Sadrita404/16-Key-Macro-Pad/IMAGES/6.png

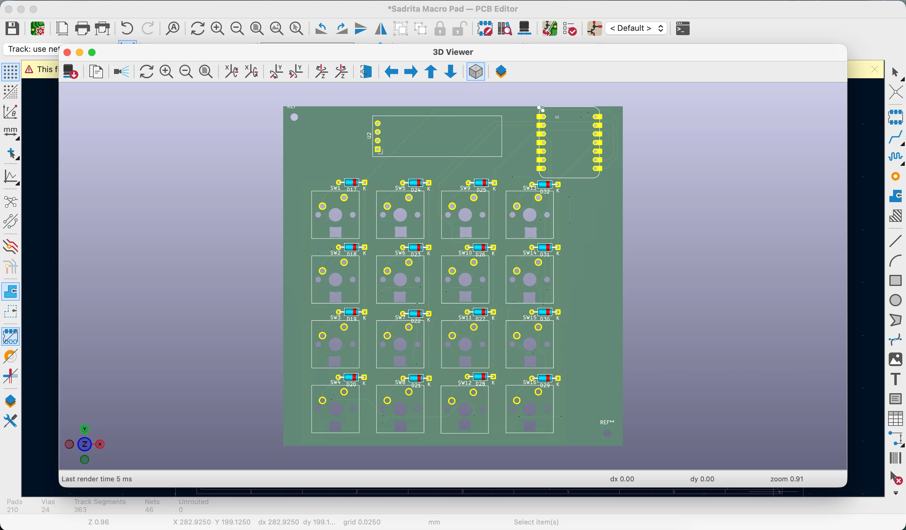
IMAGES/6.png
