Sadrita404/16-Key-Macro-Pad/IMAGES/7.png

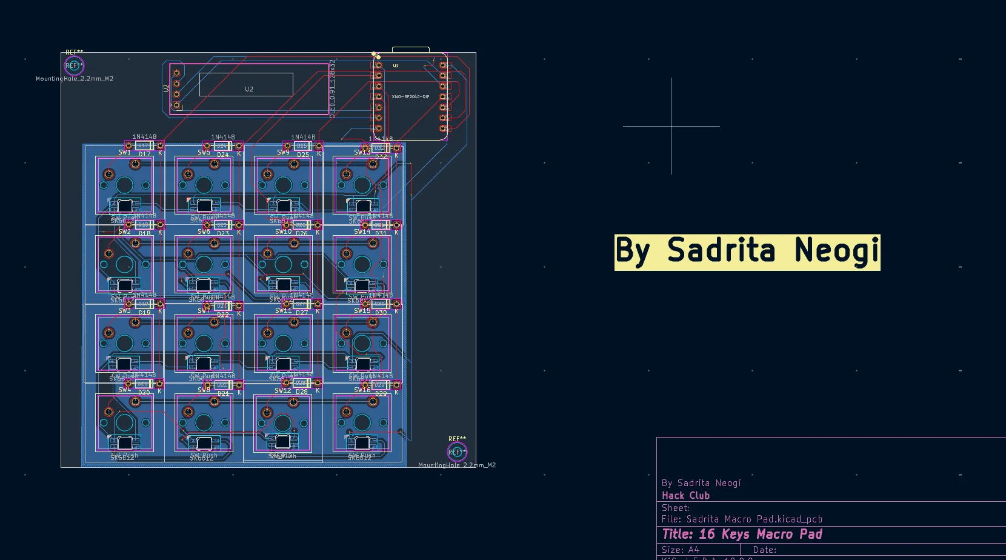
IMAGES/7.png
