Sadrita404/16-Key-Macro-Pad/BILL/1 Bill.png

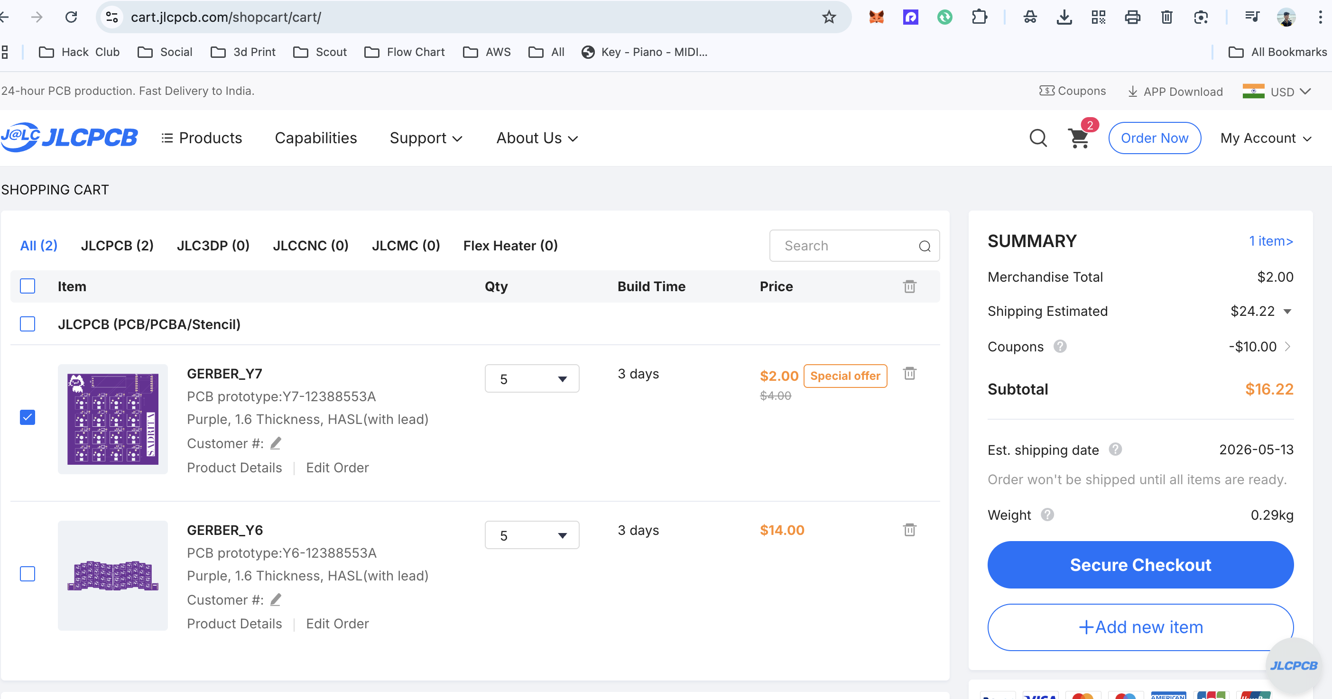
BILL/1 Bill.png
