Sadrita404/16-Key-Macro-Pad/BILL/2 Bill.png

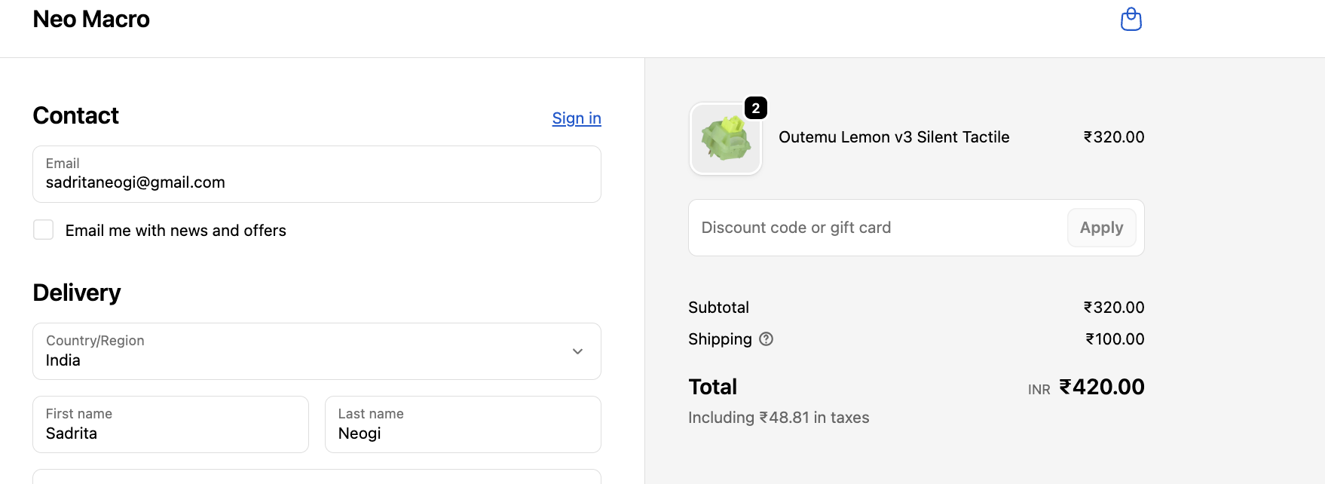
BILL/2 Bill.png
