Sadrita404/16-Key-Macro-Pad/BILL/3 Bill.png

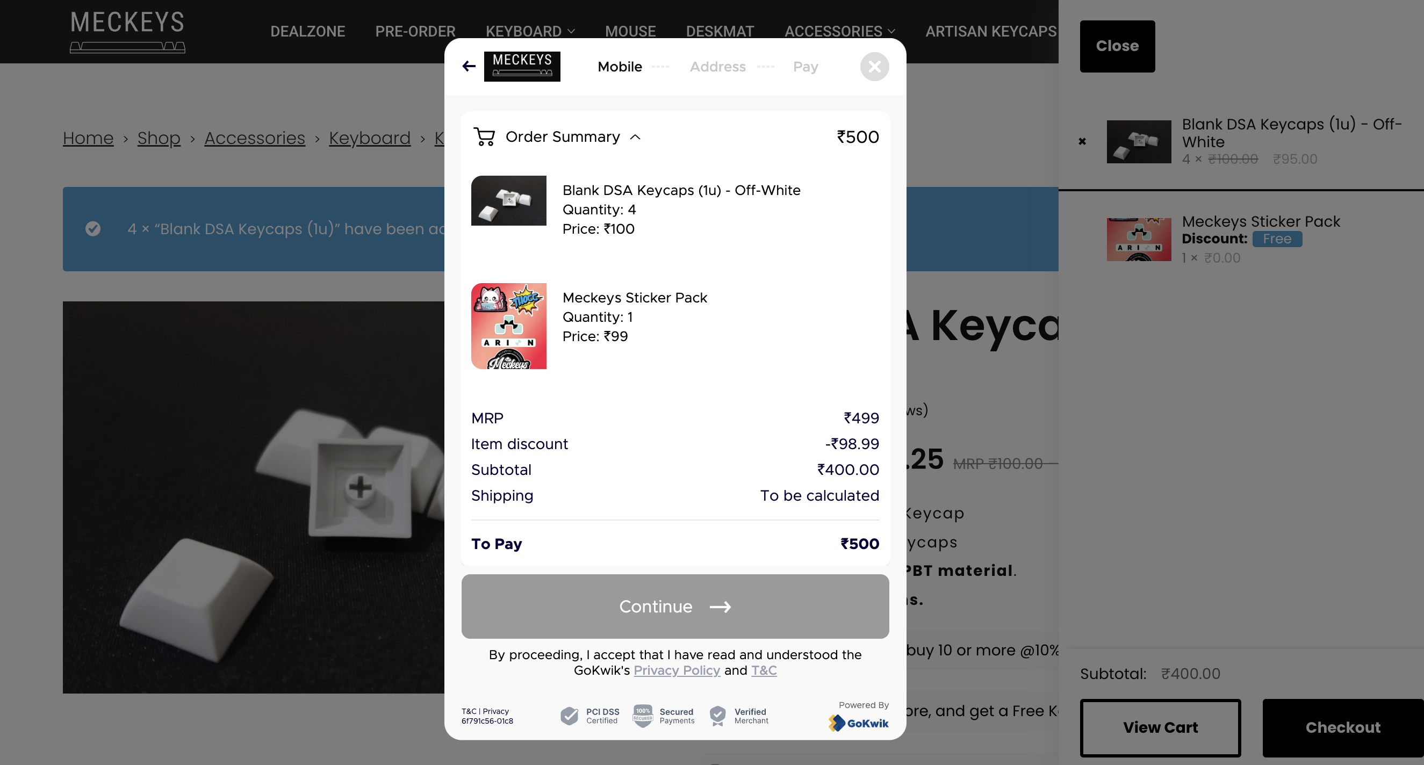
BILL/3 Bill.png
