Sadrita404/16-Key-Macro-Pad/BILL/4 Bill.png

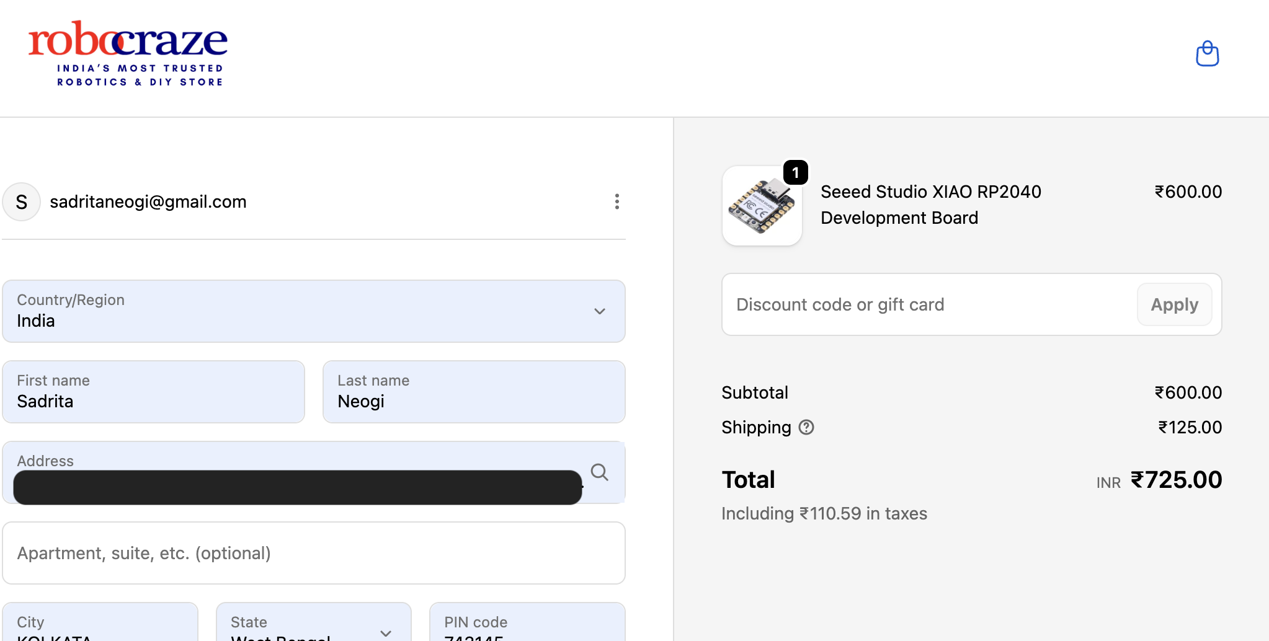
BILL/4 Bill.png
