Sadrita404/16-Key-Macro-Pad/BILL/5 Bill.png

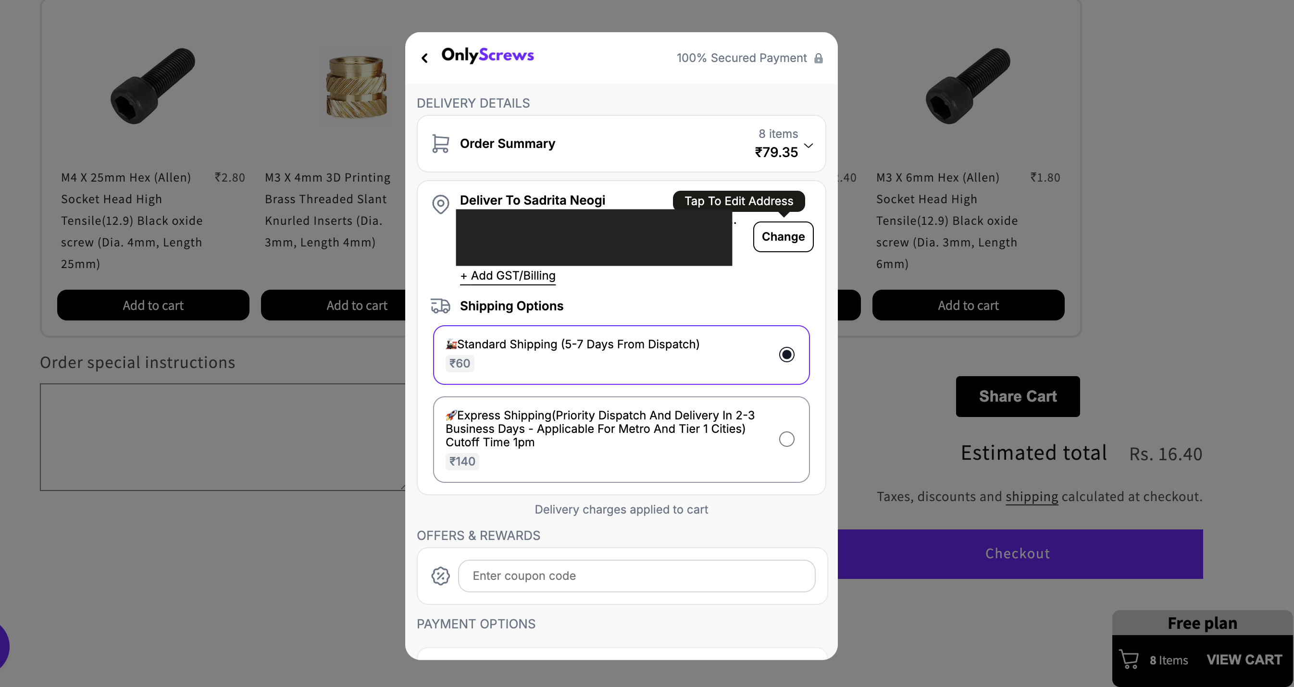
BILL/5 Bill.png
