Sadrita404/16-Key-Macro-Pad/BILL/6 Bill.png

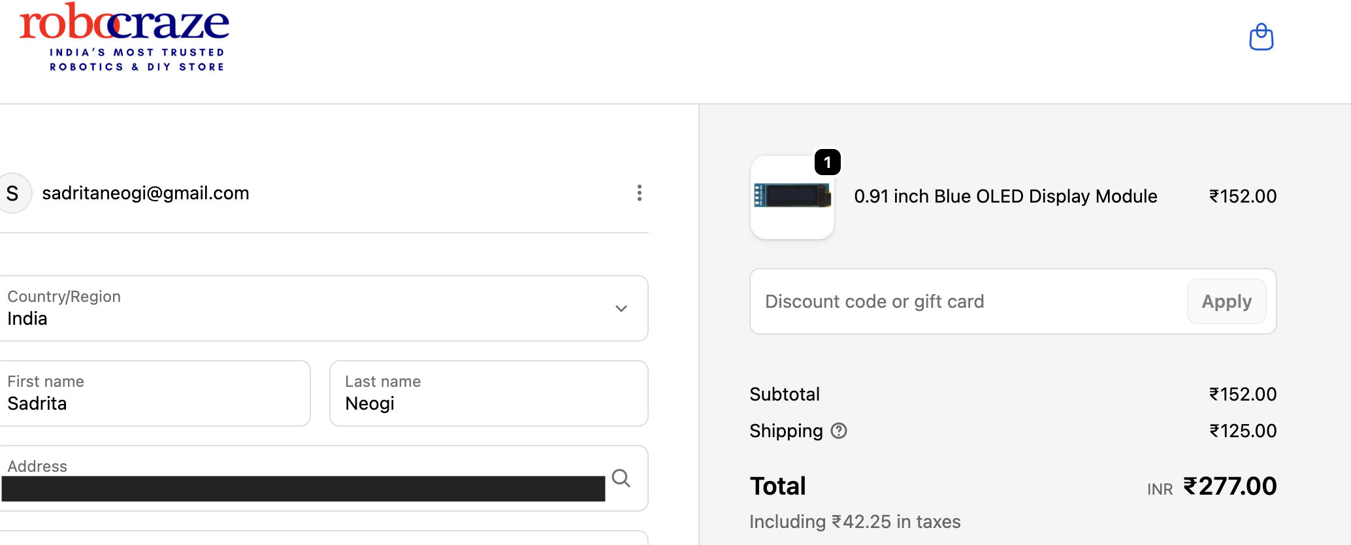
BILL/6 Bill.png
