Sadrita404/16-Key-Macro-Pad/BILL/7 Bill.png

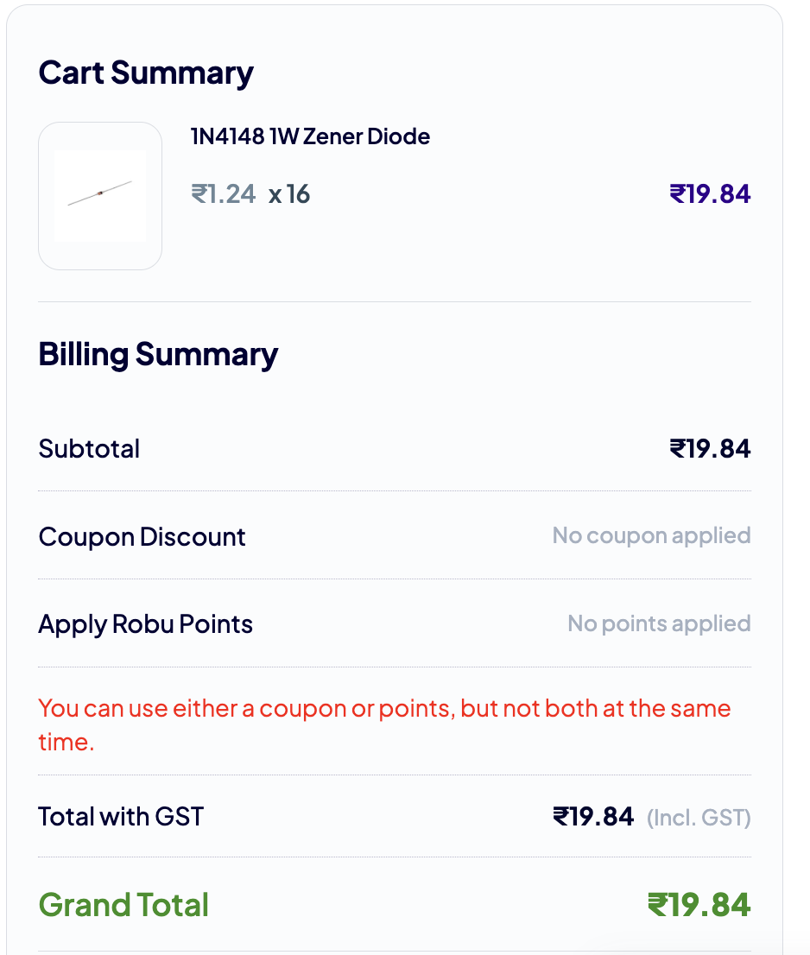
BILL/7 Bill.png
