Sadrita404/16-Key-Macro-Pad/IMAGES/1.png

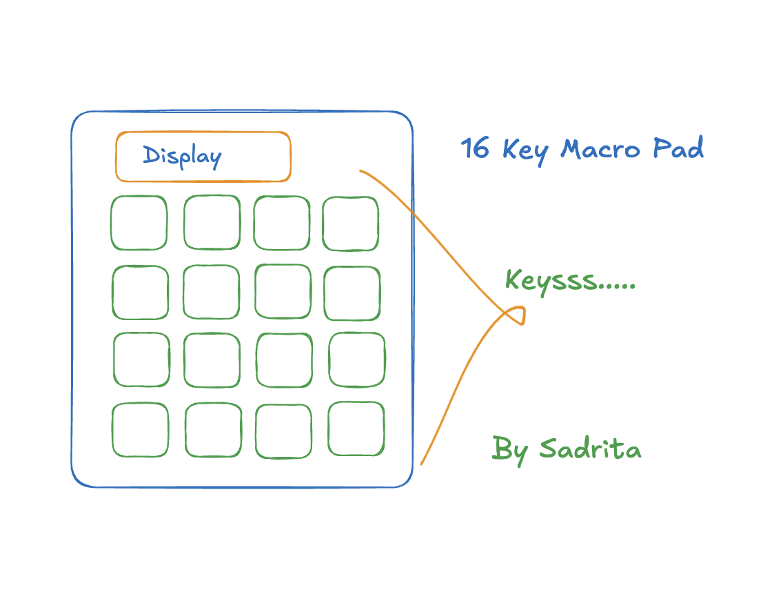
IMAGES/1.png
