Sadrita404/16-Key-Macro-Pad/IMAGES/2.png

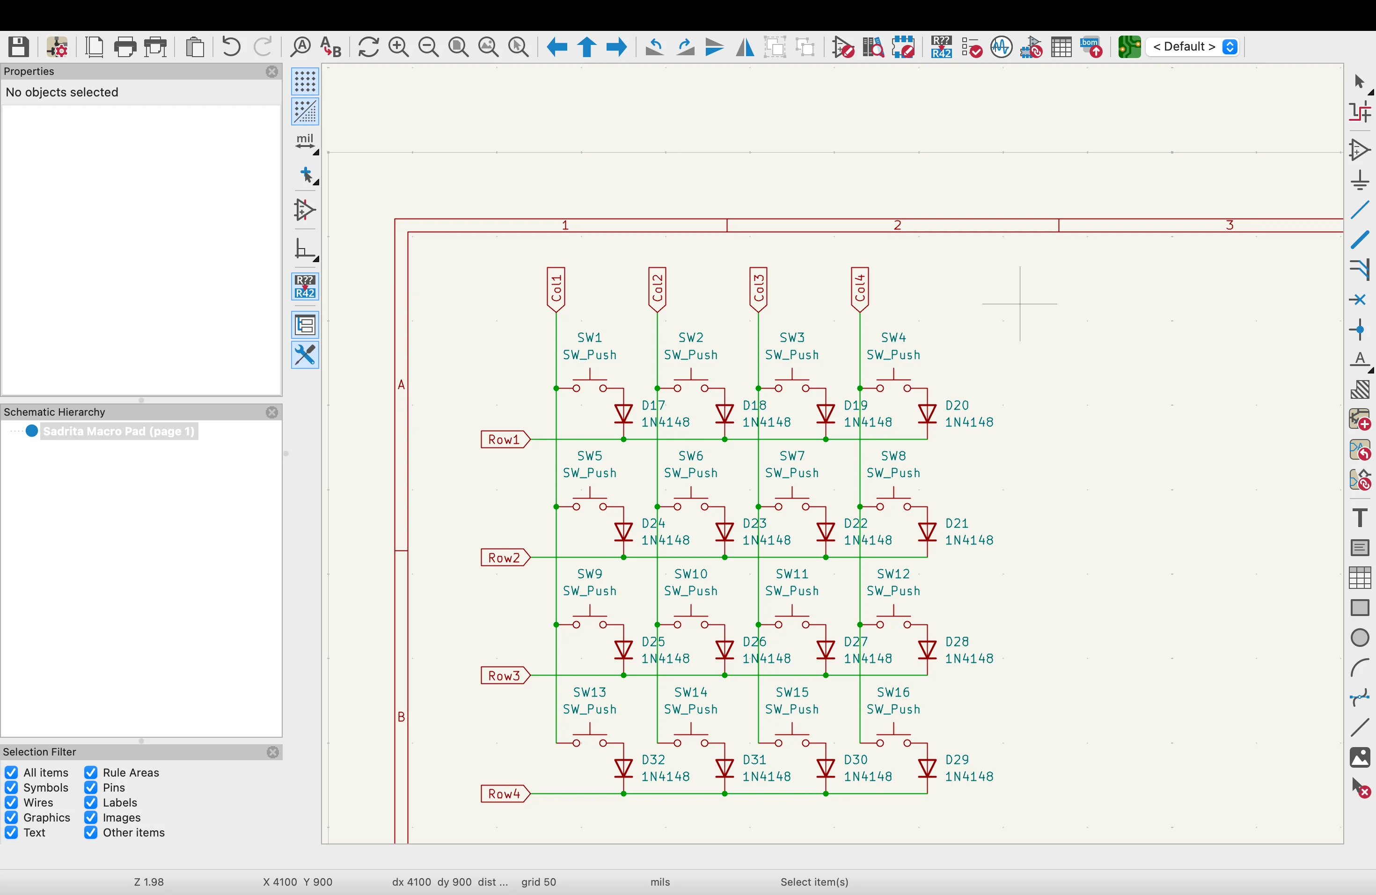
IMAGES/2.png
