Sadrita404/16-Key-Macro-Pad/IMAGES/3.png

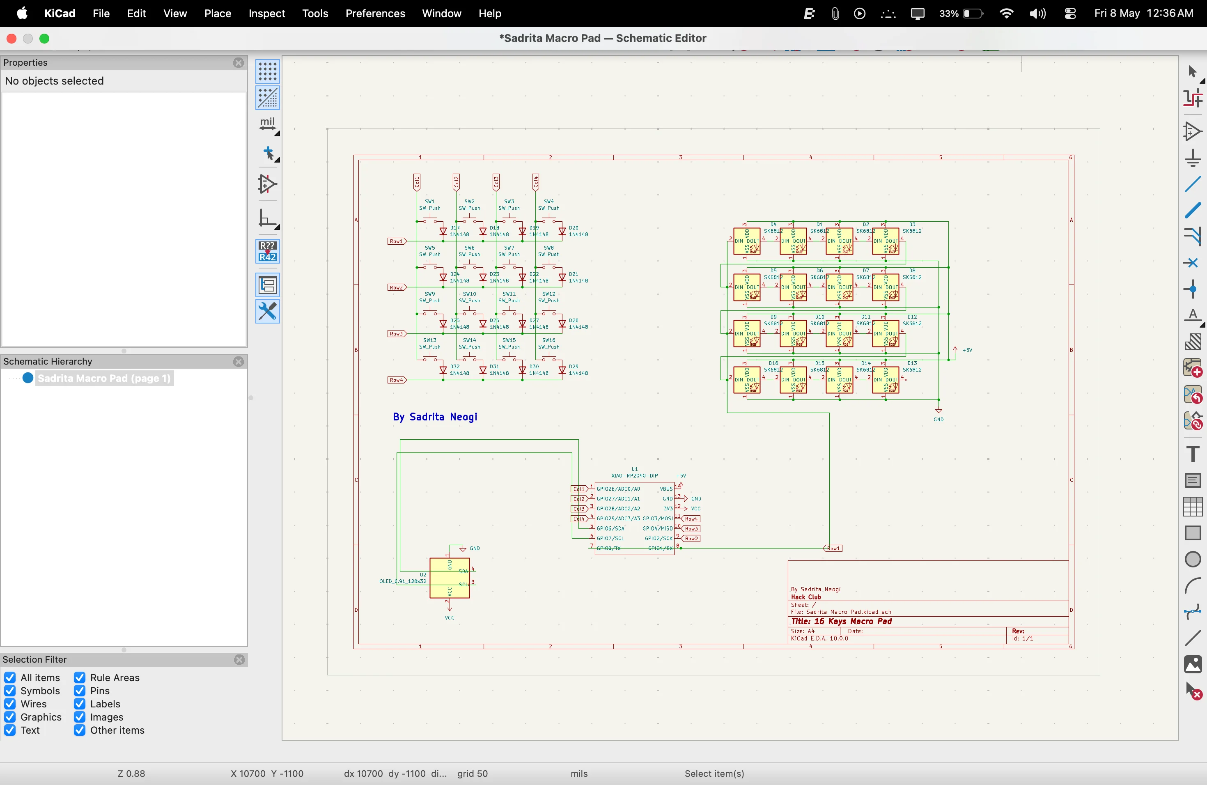
IMAGES/3.png
