Sadrita404/16-Key-Macro-Pad/IMAGES/4.png

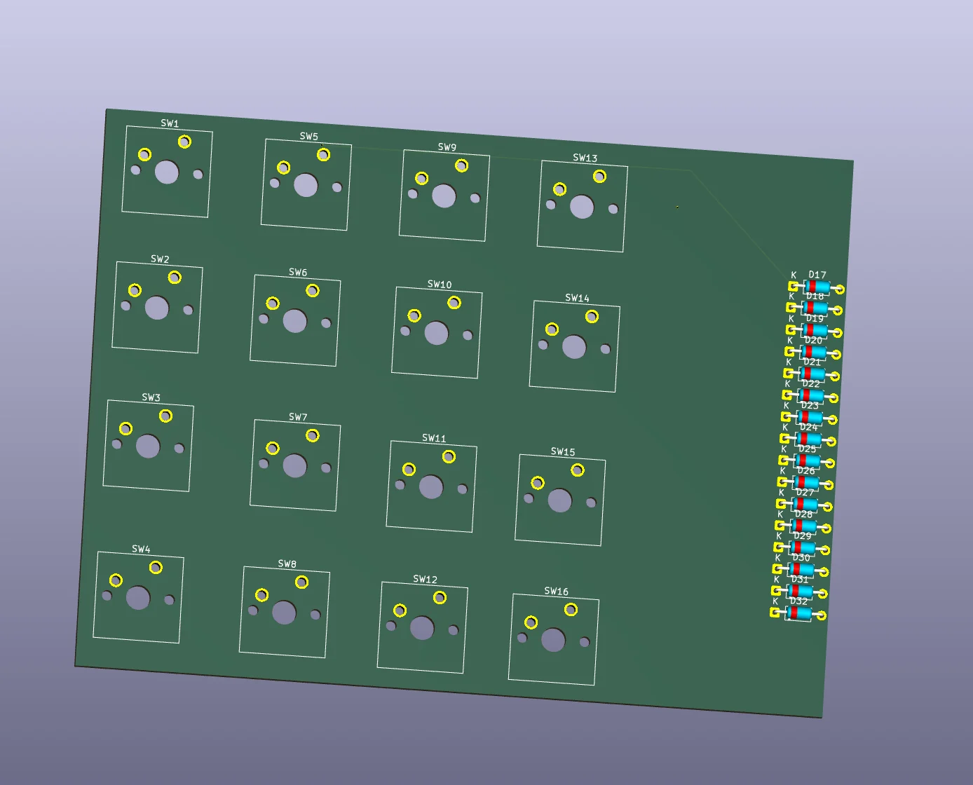
IMAGES/4.png
