Sadrita404/16-Key-Macro-Pad/IMAGES/5.png

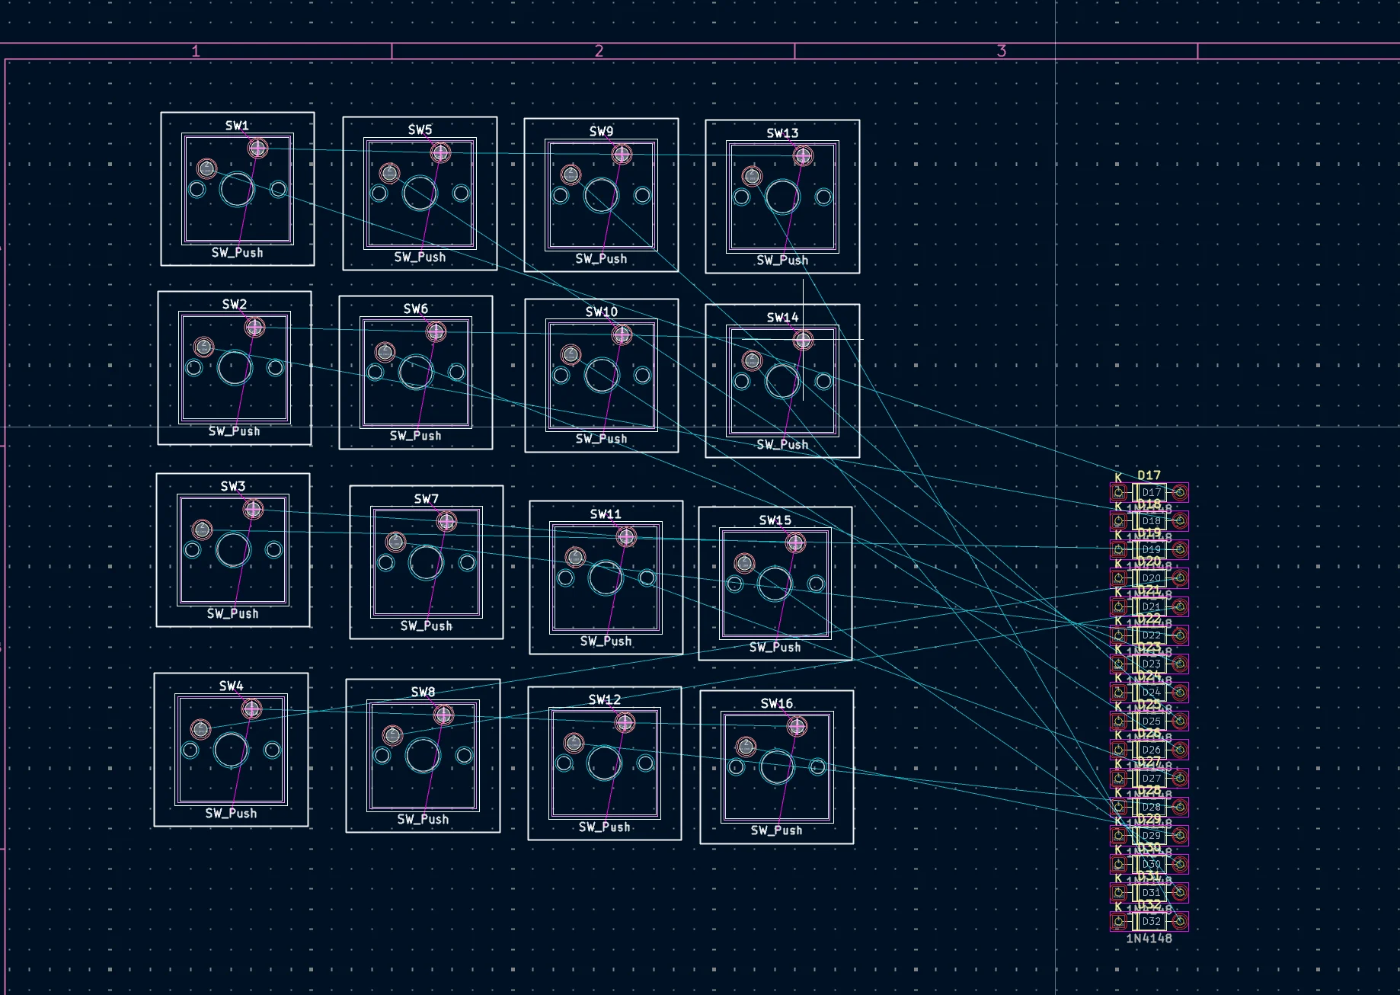
IMAGES/5.png
