Sadrita404/16-Key-Macro-Pad/IMAGES/8.png

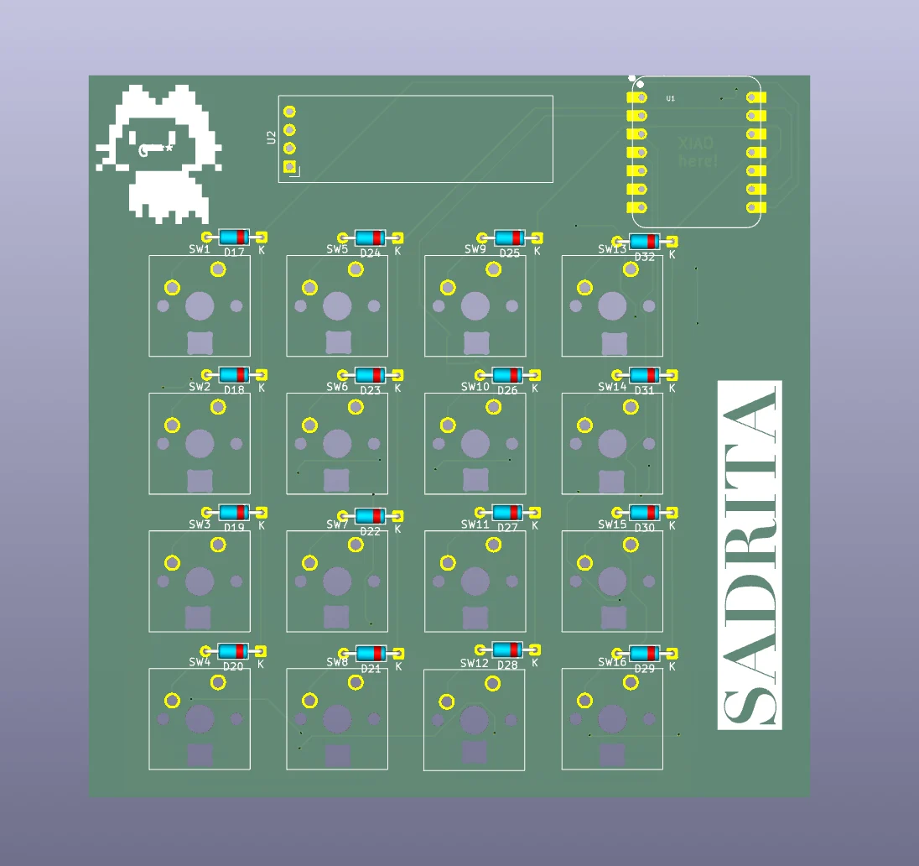
IMAGES/8.png
