Sadrita404/16-Key-Macro-Pad/IMAGES/9.png

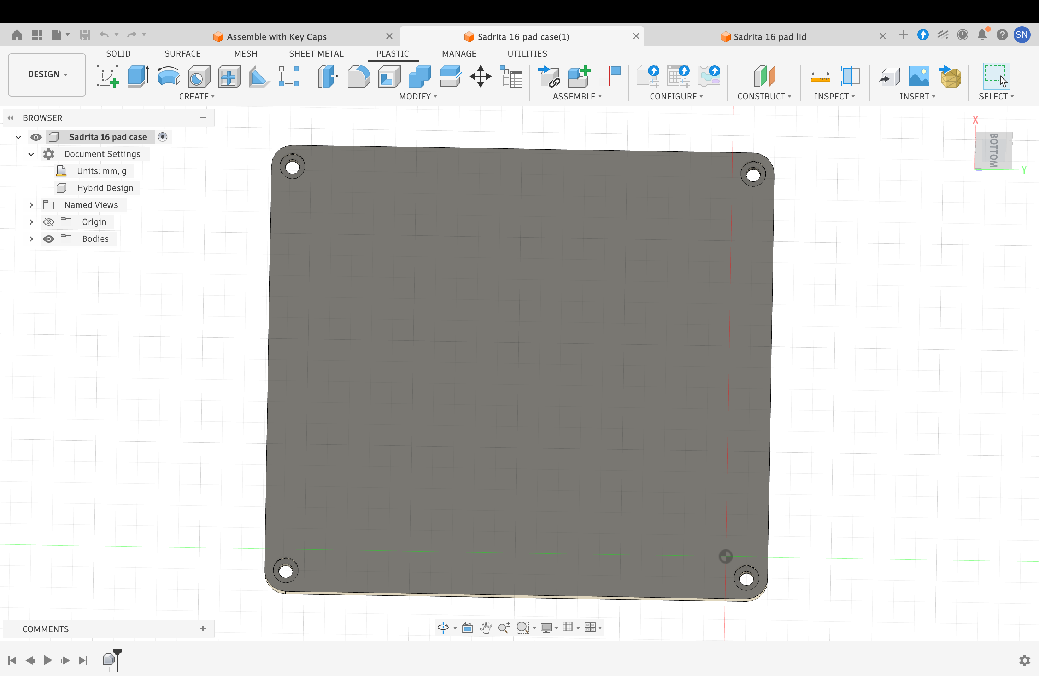
IMAGES/9.png
