Sadrita404/16-Key-Macro-Pad/IMAGES/10.png

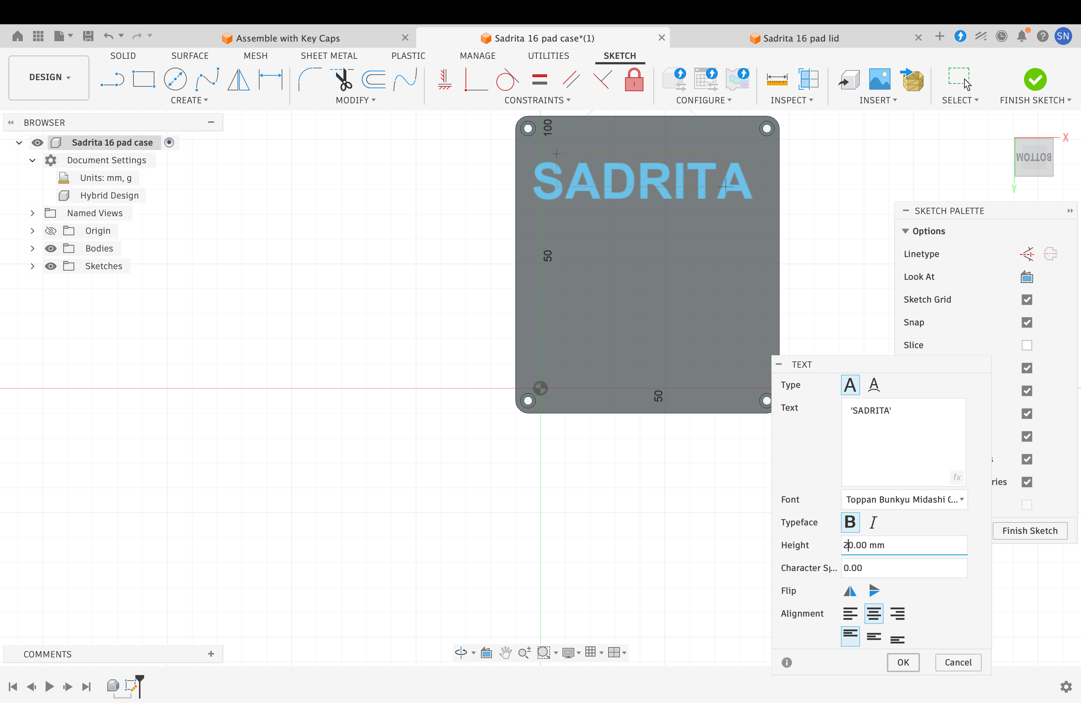
IMAGES/10.png
