Sadrita404/16-Key-Macro-Pad/IMAGES/11.png

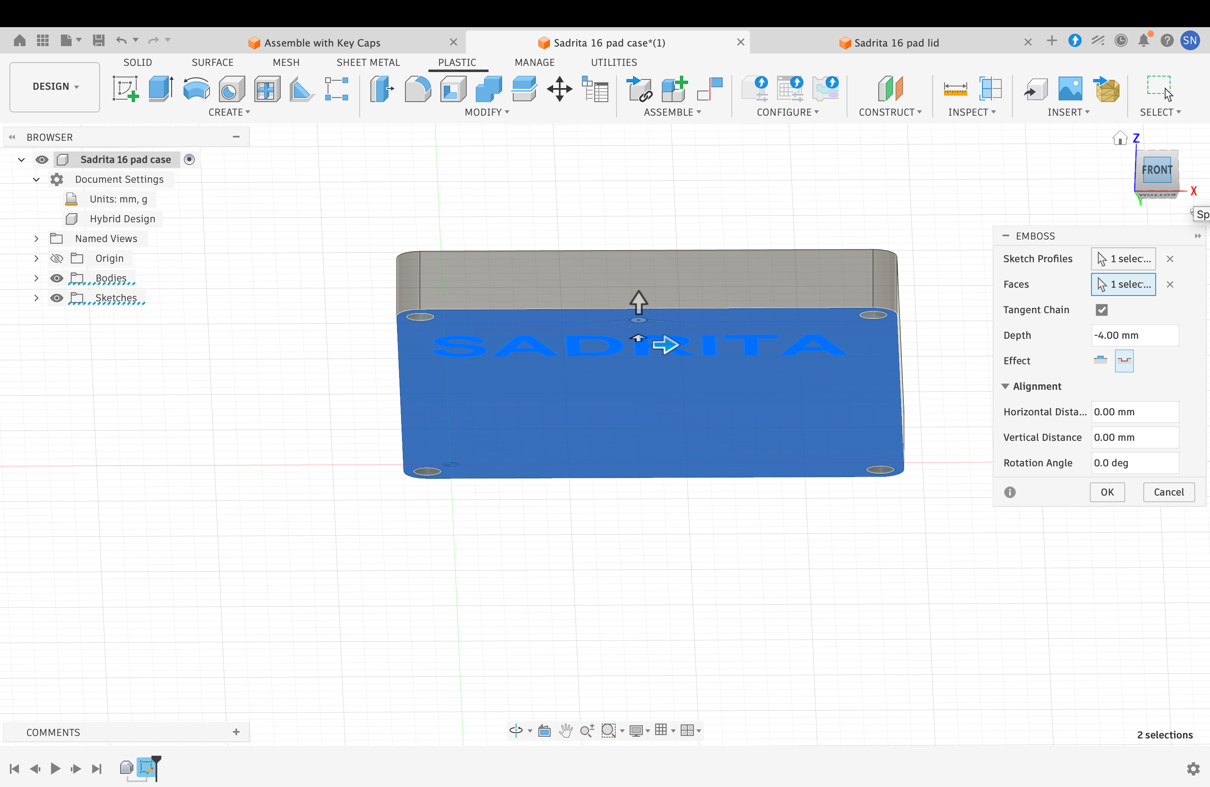
IMAGES/11.png
