Sadrita404/16-Key-Macro-Pad/IMAGES/12.png

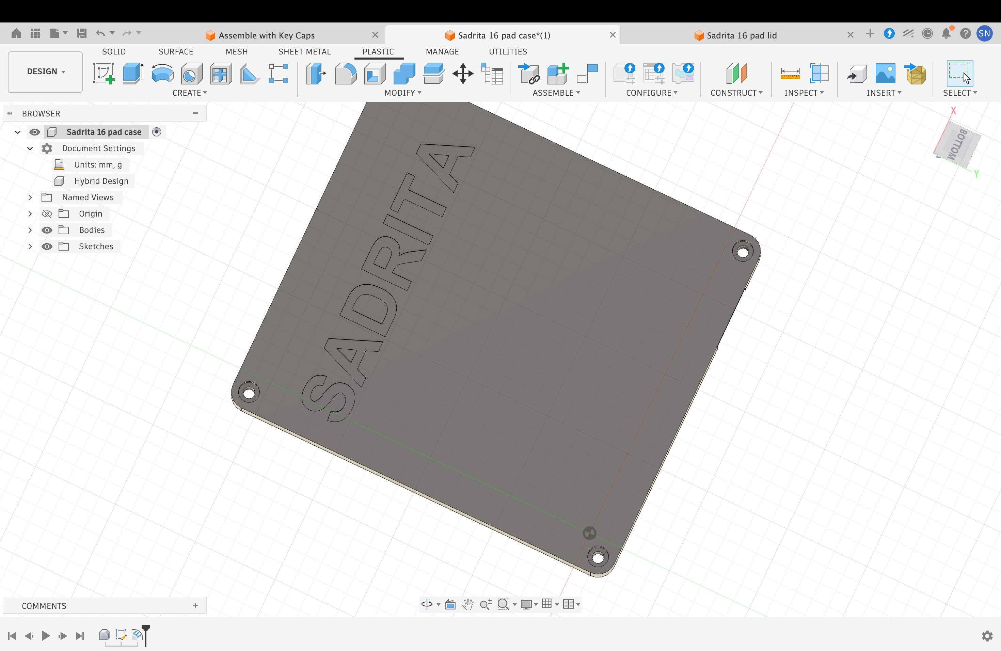
IMAGES/12.png
