Sadrita404/16-Key-Macro-Pad/IMAGES/13.png

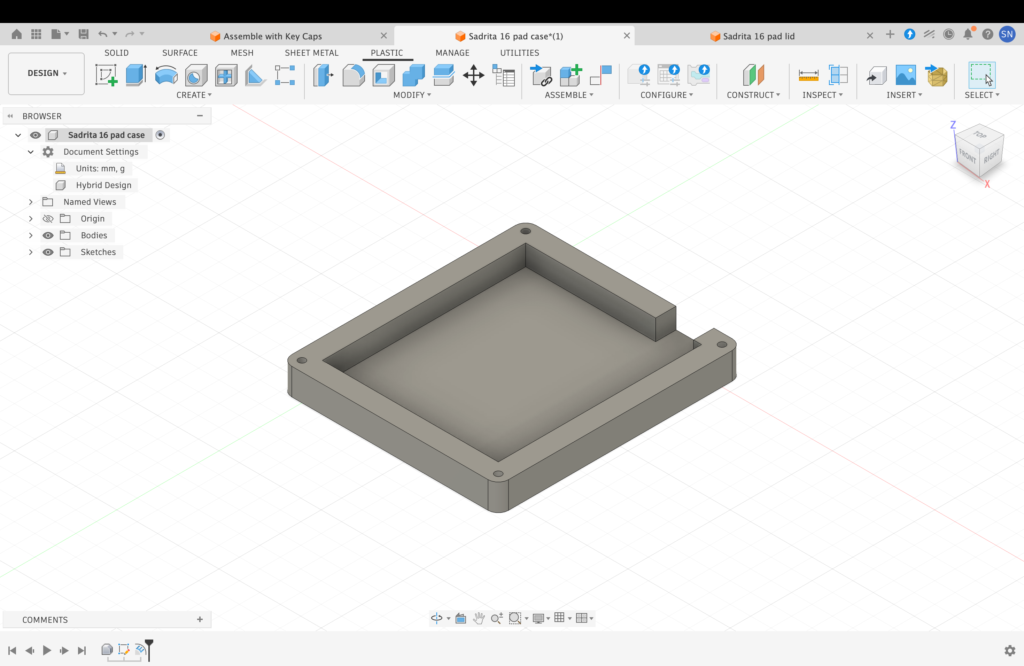
IMAGES/13.png
