Sadrita404/16-Key-Macro-Pad/IMAGES/14.png

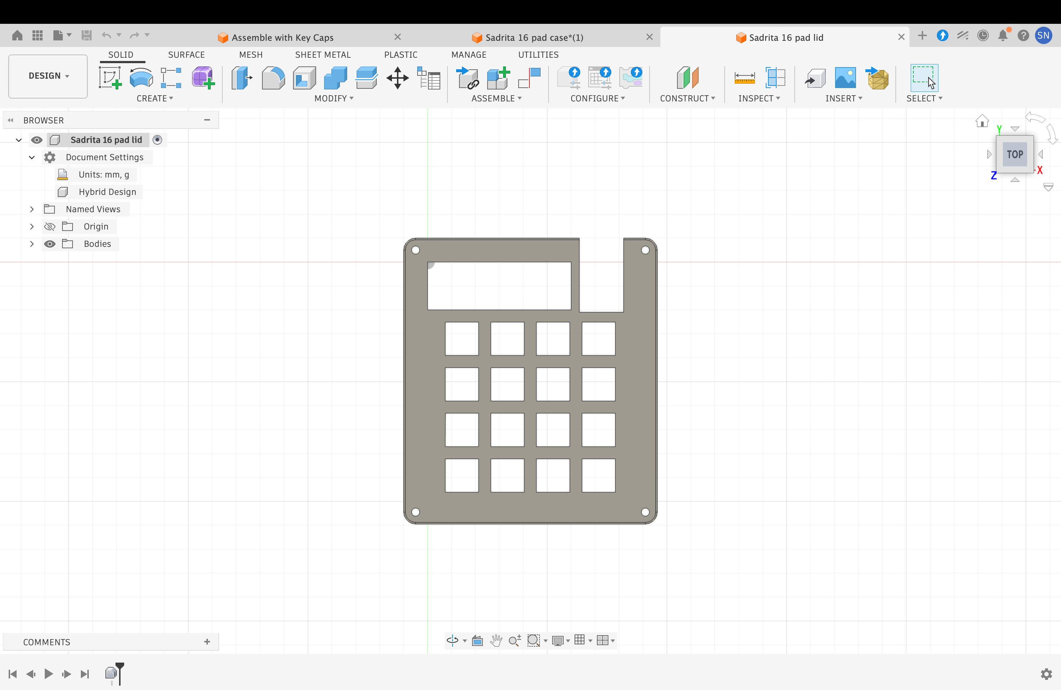
IMAGES/14.png
