Sadrita404/16-Key-Macro-Pad/IMAGES/15.png

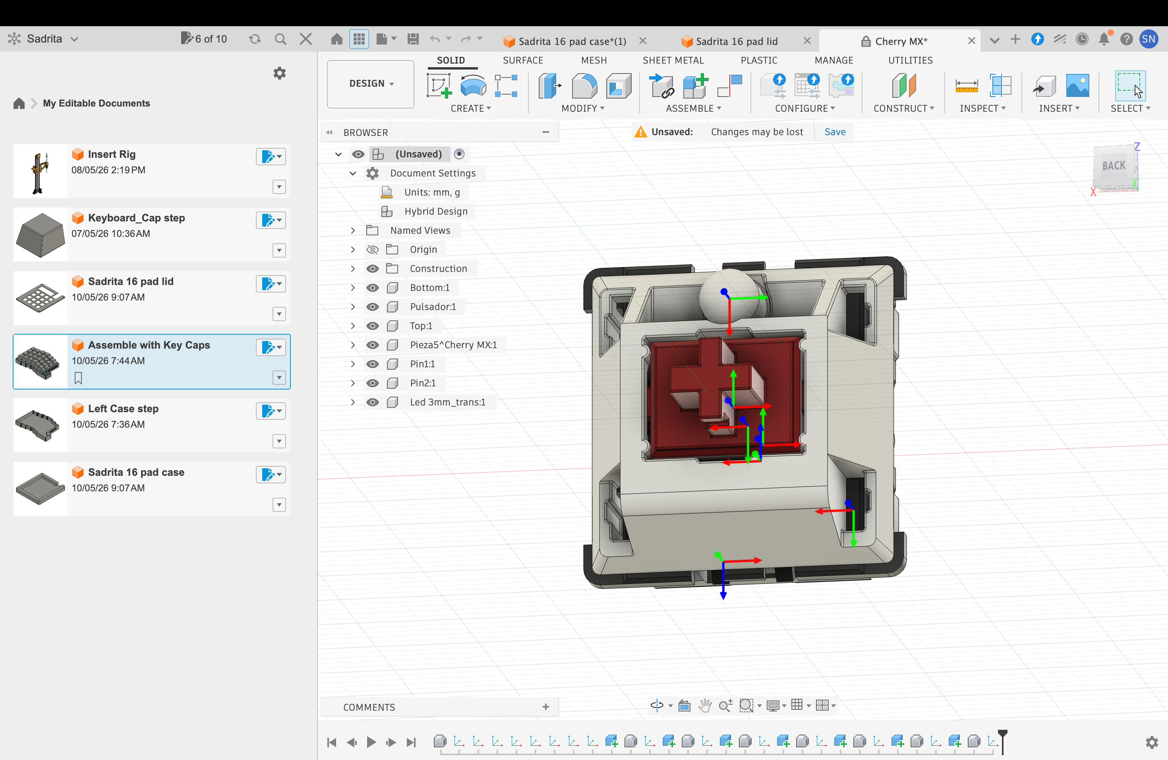
IMAGES/15.png
