Sadrita404/16-Key-Macro-Pad/IMAGES/16.png

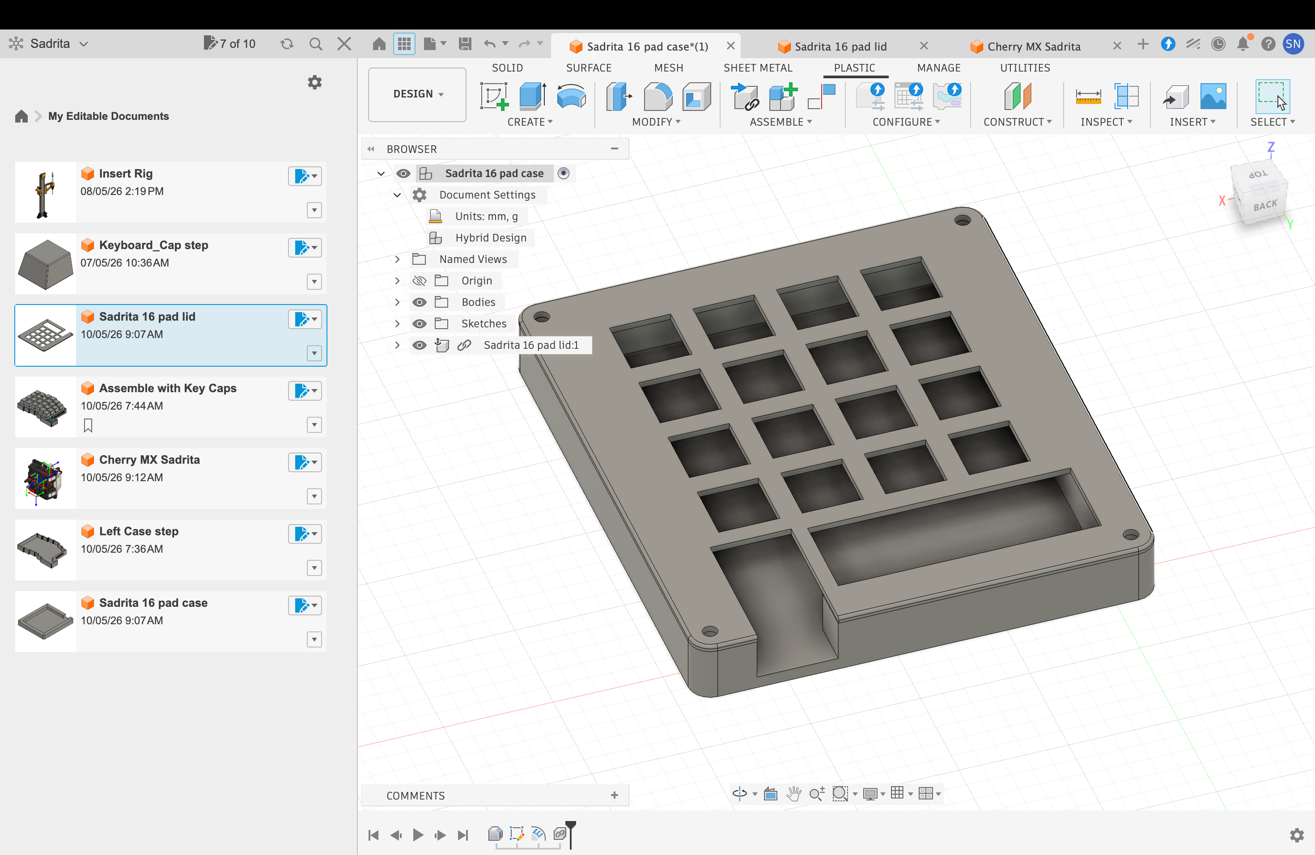
IMAGES/16.png
