Sadrita404/16-Key-Macro-Pad/IMAGES/17.png

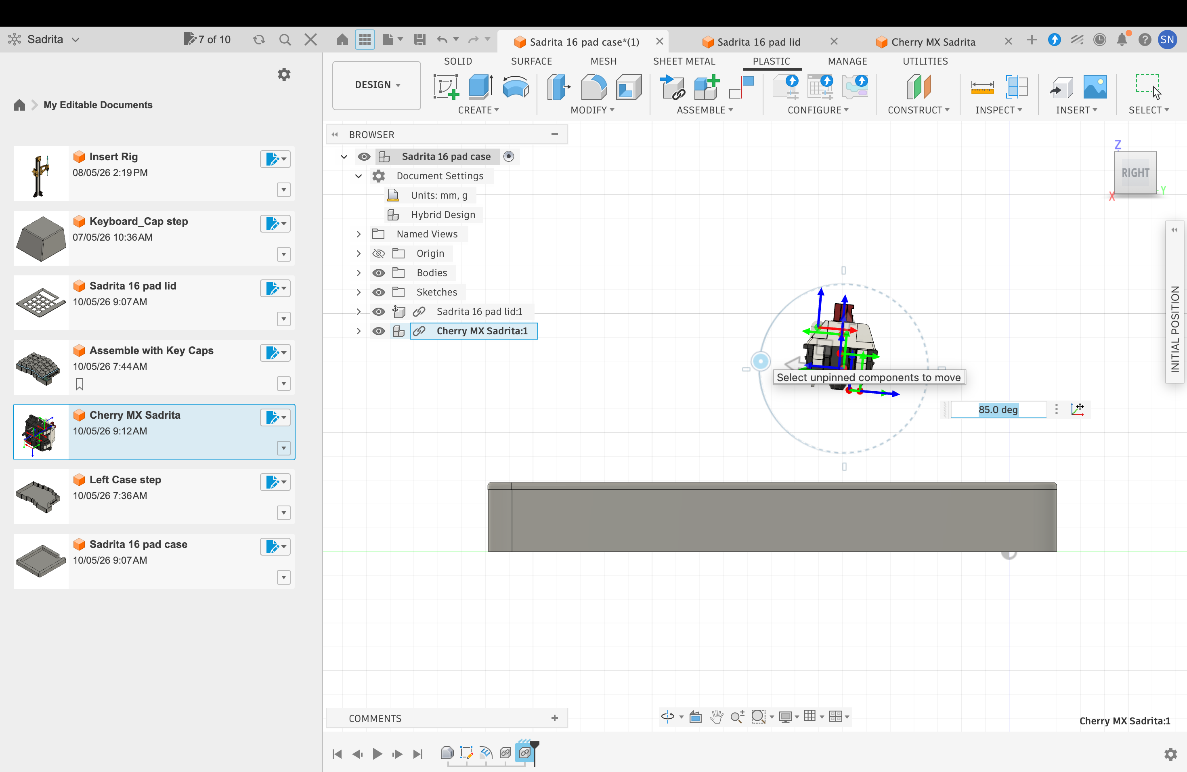
IMAGES/17.png
