Sadrita404/16-Key-Macro-Pad/IMAGES/18.png

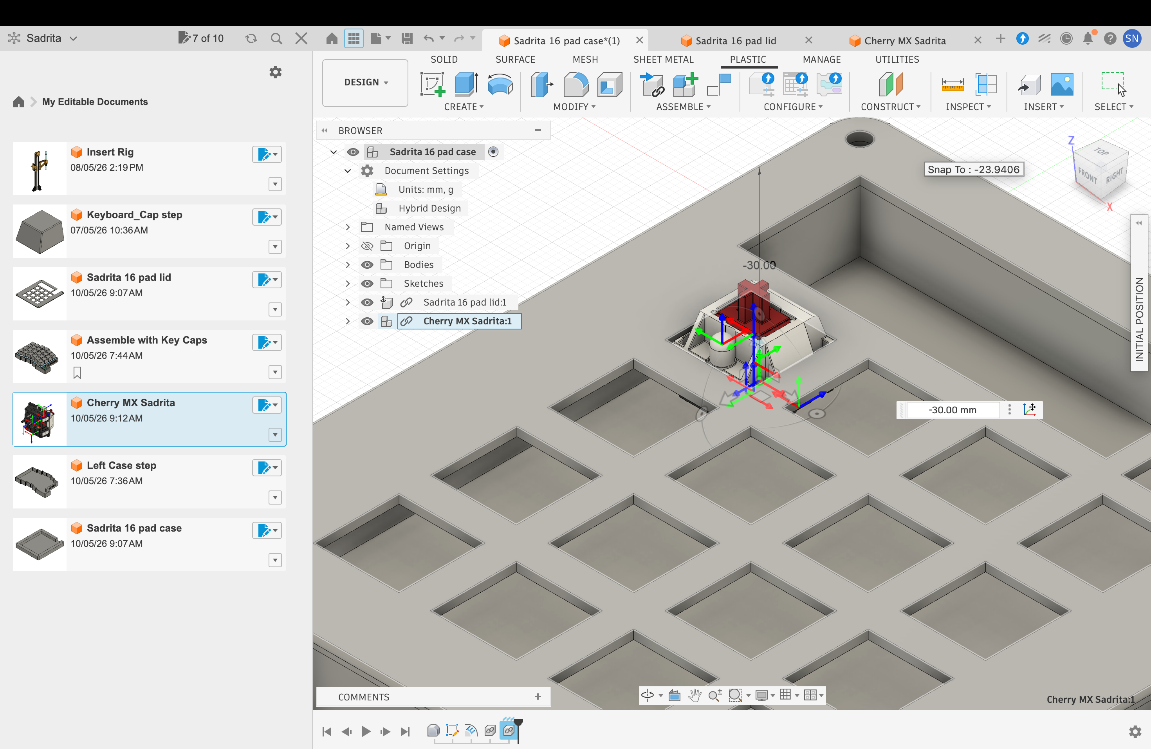
IMAGES/18.png
