Sadrita404/16-Key-Macro-Pad/IMAGES/19.png

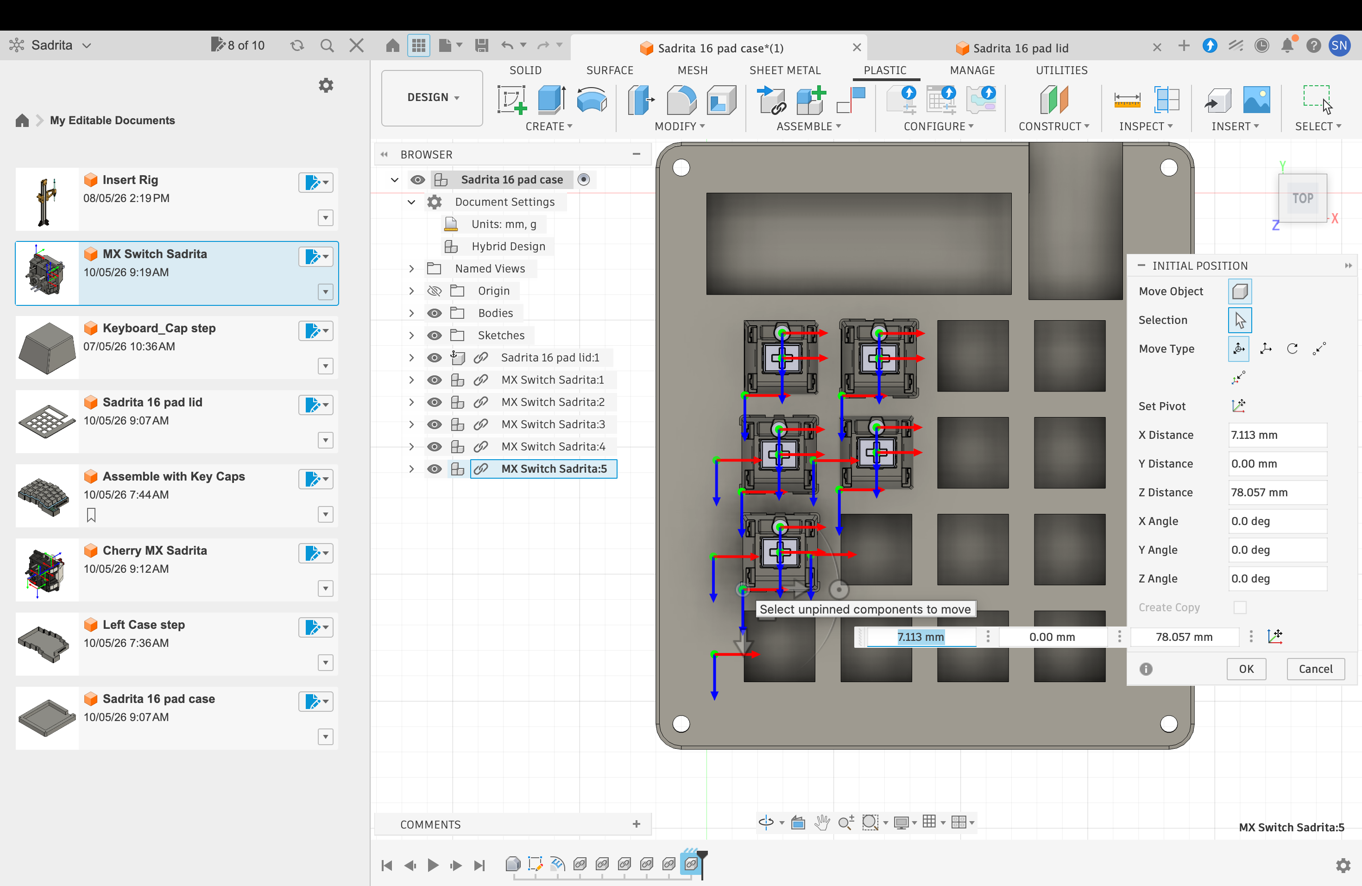
IMAGES/19.png
