Sadrita404/16-Key-Macro-Pad/IMAGES/20.png

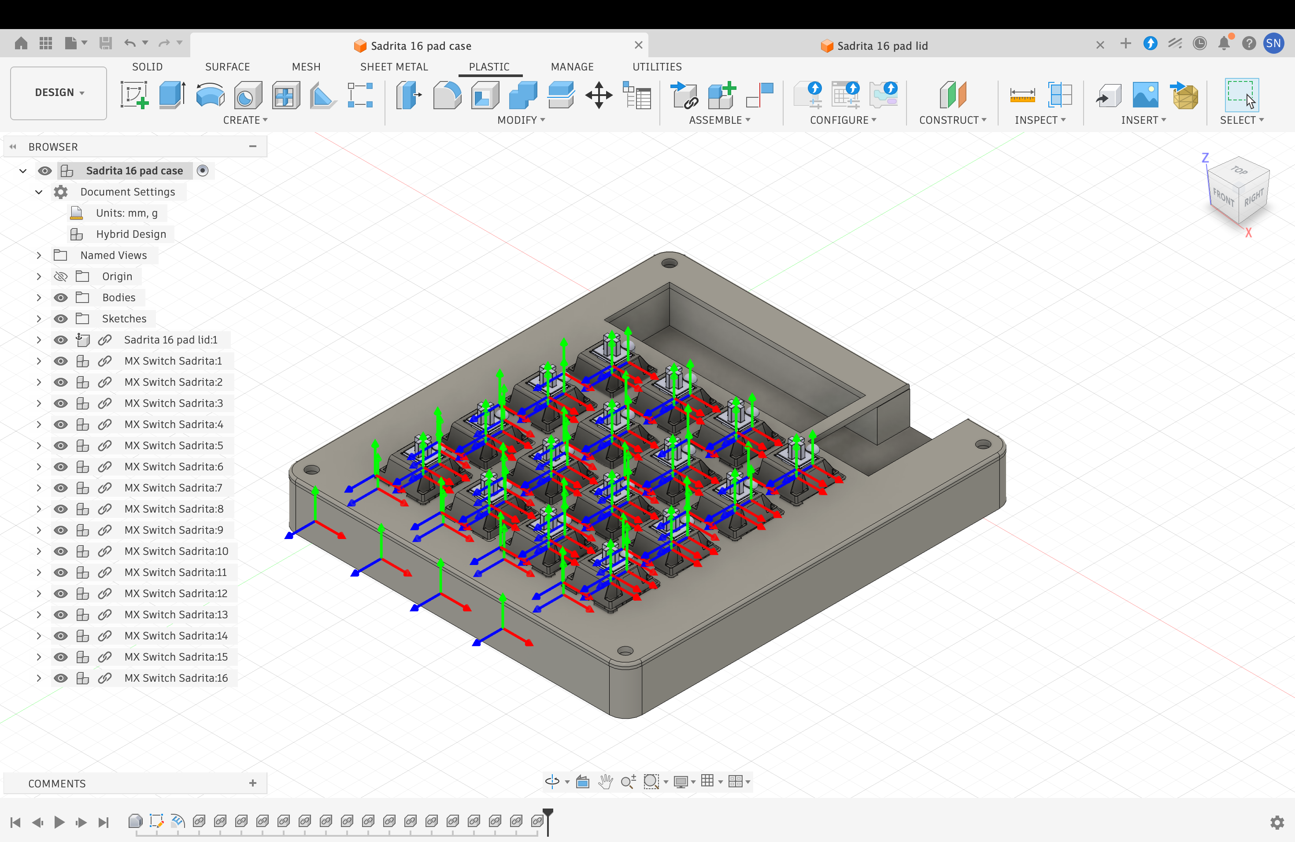
IMAGES/20.png
