Sadrita404/16-Key-Macro-Pad/IMAGES/21.png

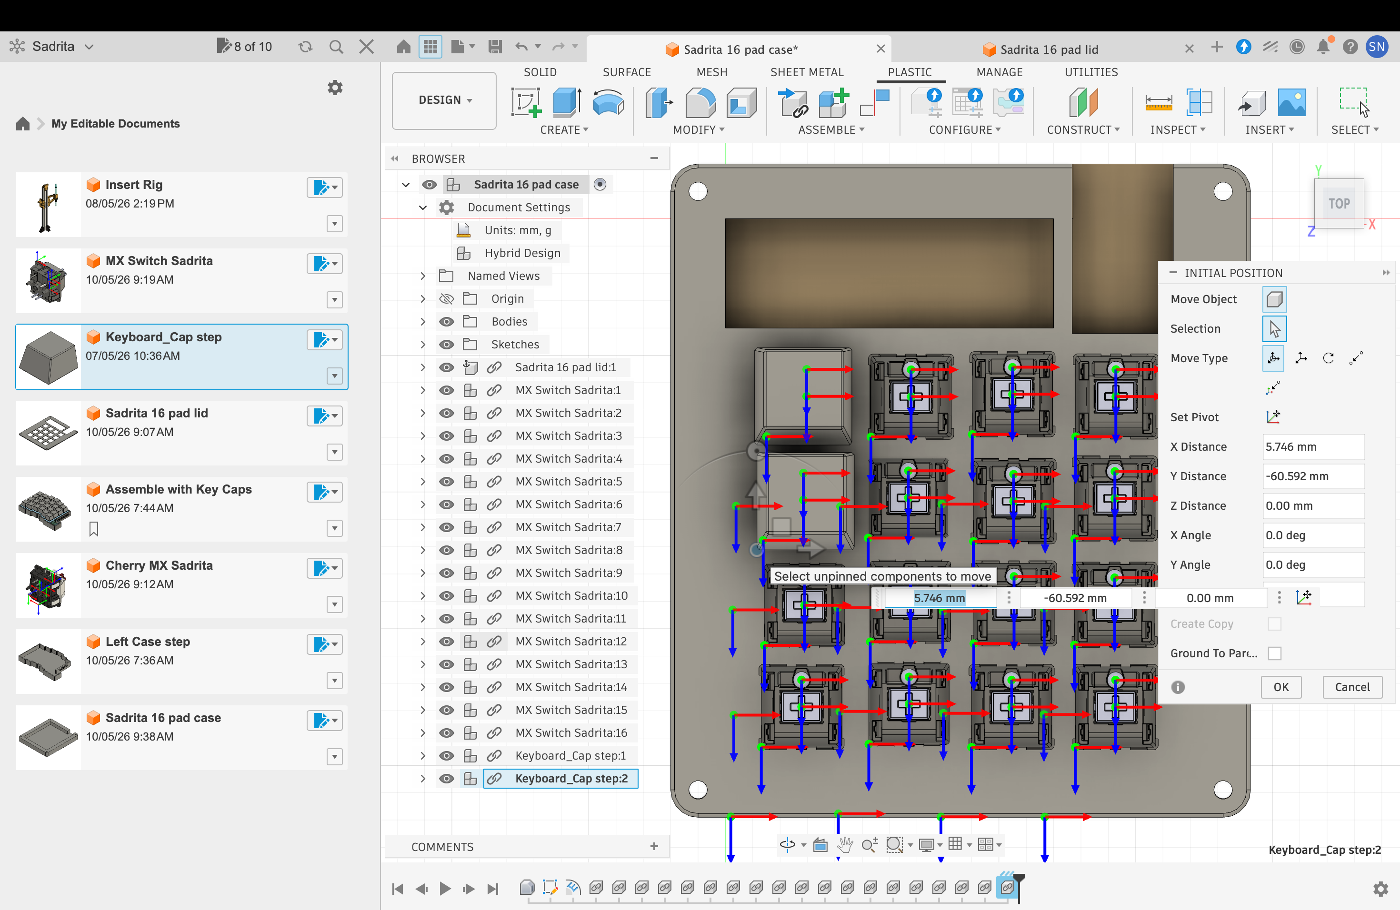
IMAGES/21.png
