Sadrita404/16-Key-Macro-Pad/IMAGES/22.png

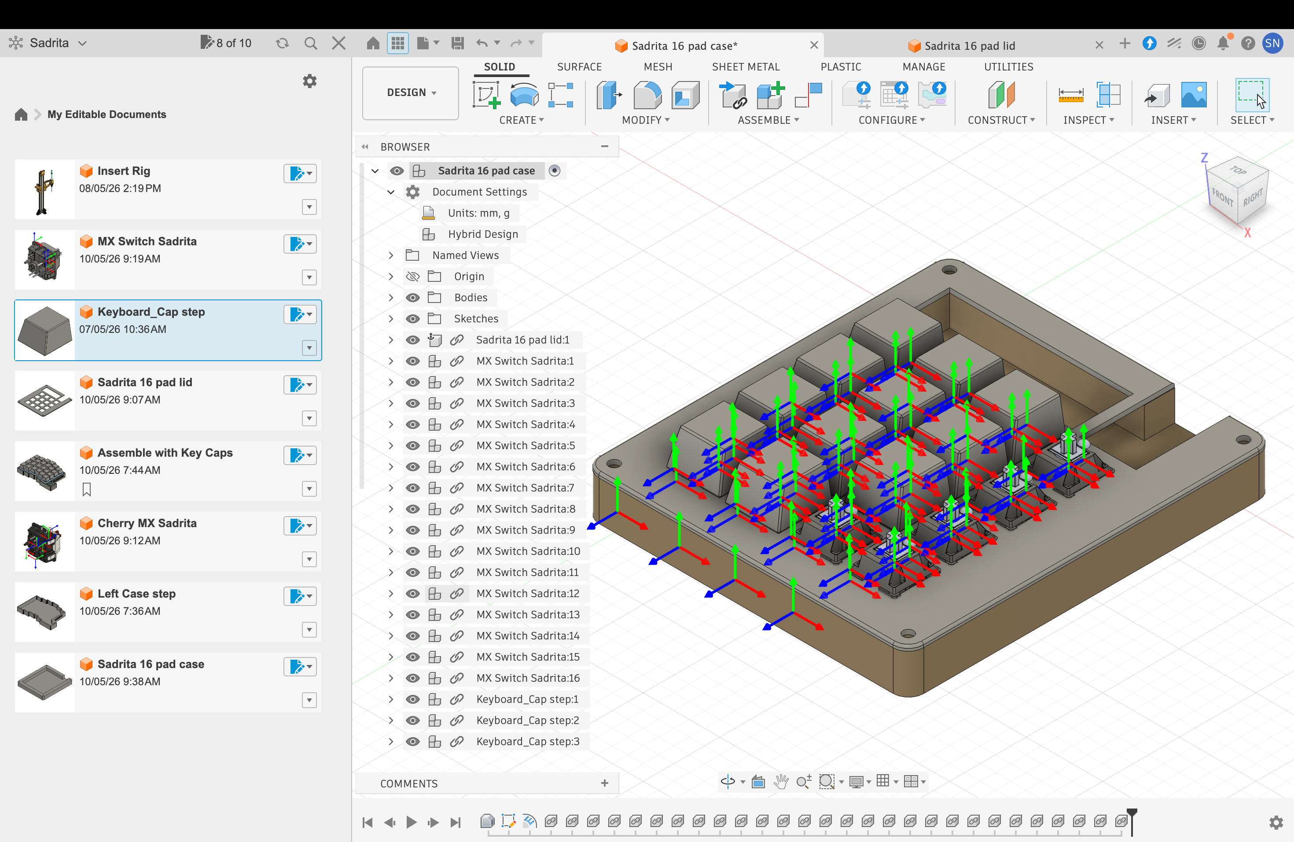
IMAGES/22.png
