Sadrita404/16-Key-Macro-Pad/IMAGES/23.png

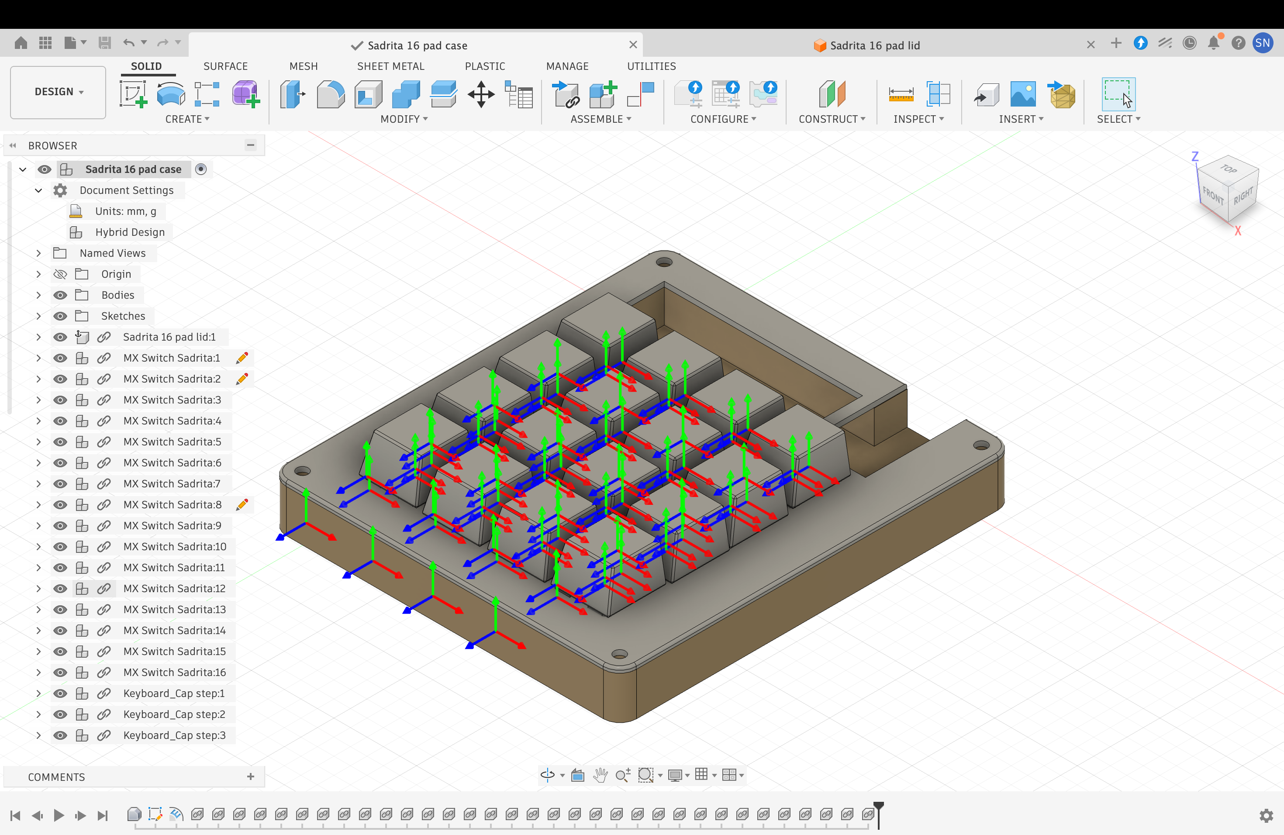
IMAGES/23.png
