Sadrita404/16-Key-Macro-Pad/IMAGES/24.png

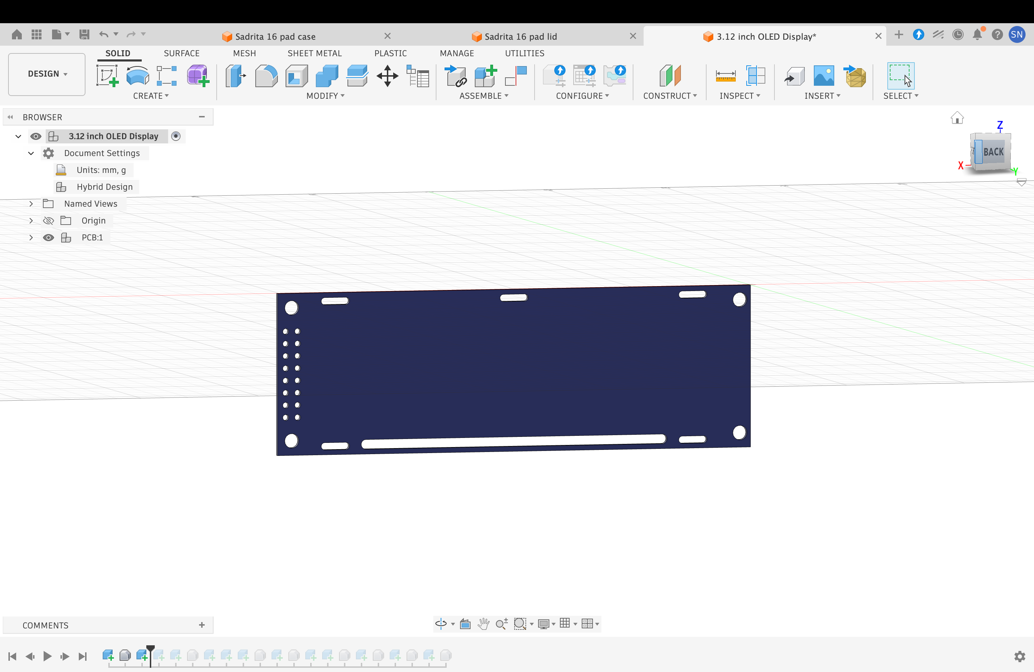
IMAGES/24.png
