Sadrita404/16-Key-Macro-Pad/IMAGES/25.png

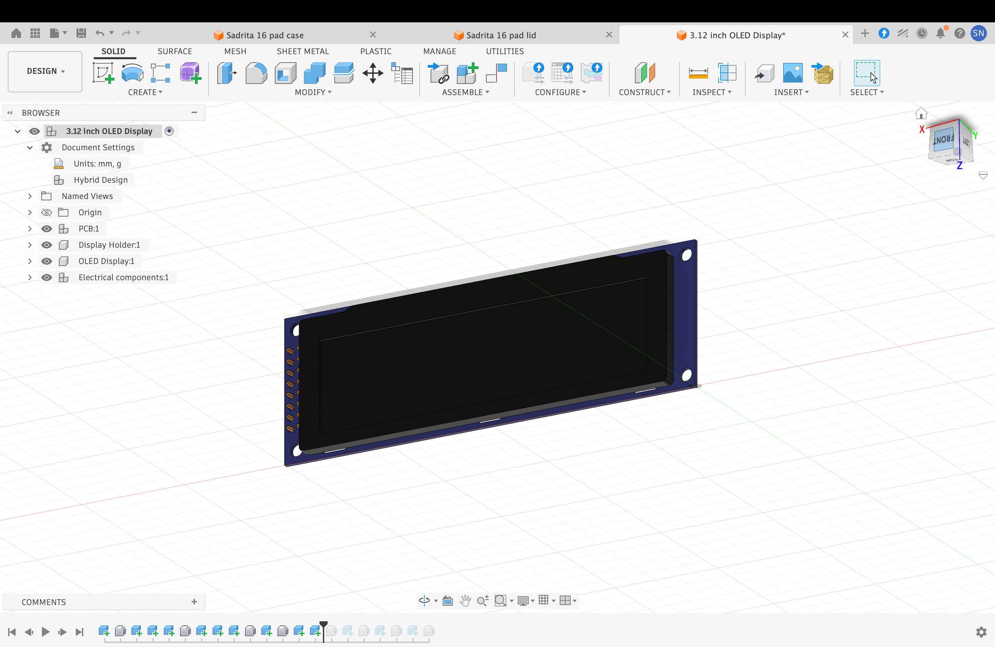
IMAGES/25.png
