Sadrita404/16-Key-Macro-Pad/IMAGES/26.png

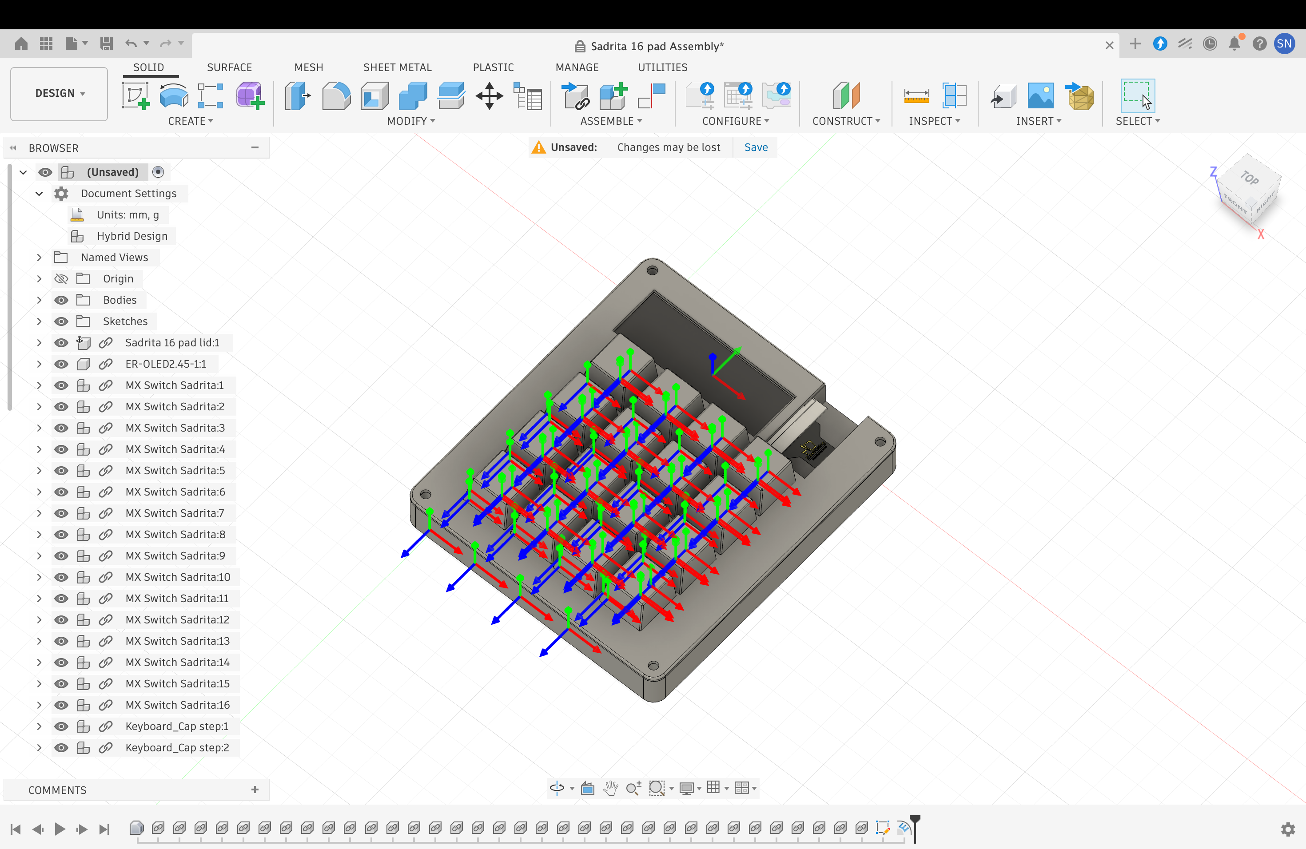
IMAGES/26.png
