Sadrita404/16-Key-Macro-Pad/IMAGES/27.png

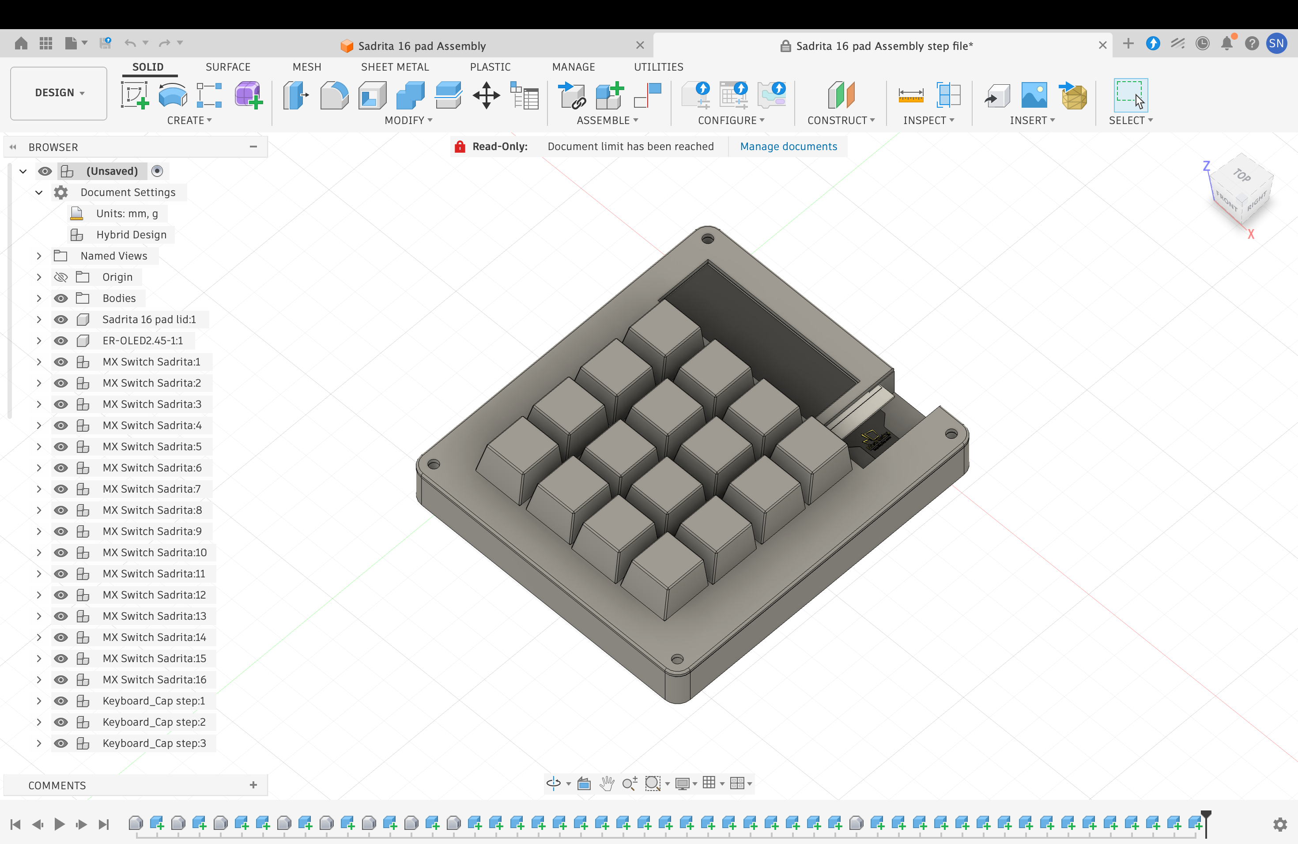
IMAGES/27.png
