Sadrita404/16-Key-Macro-Pad/IMAGES/28.png

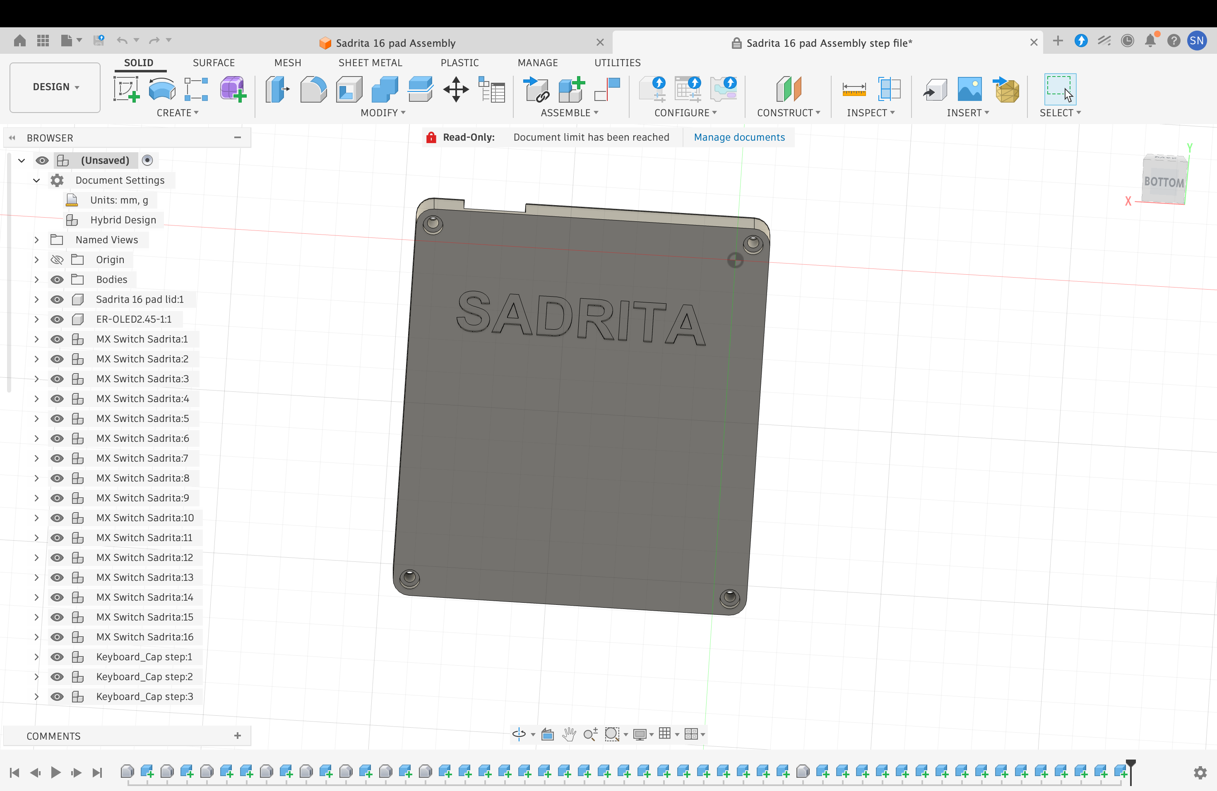
IMAGES/28.png
