Sadrita404/16-Key-Macro-Pad/IMAGES/29.png

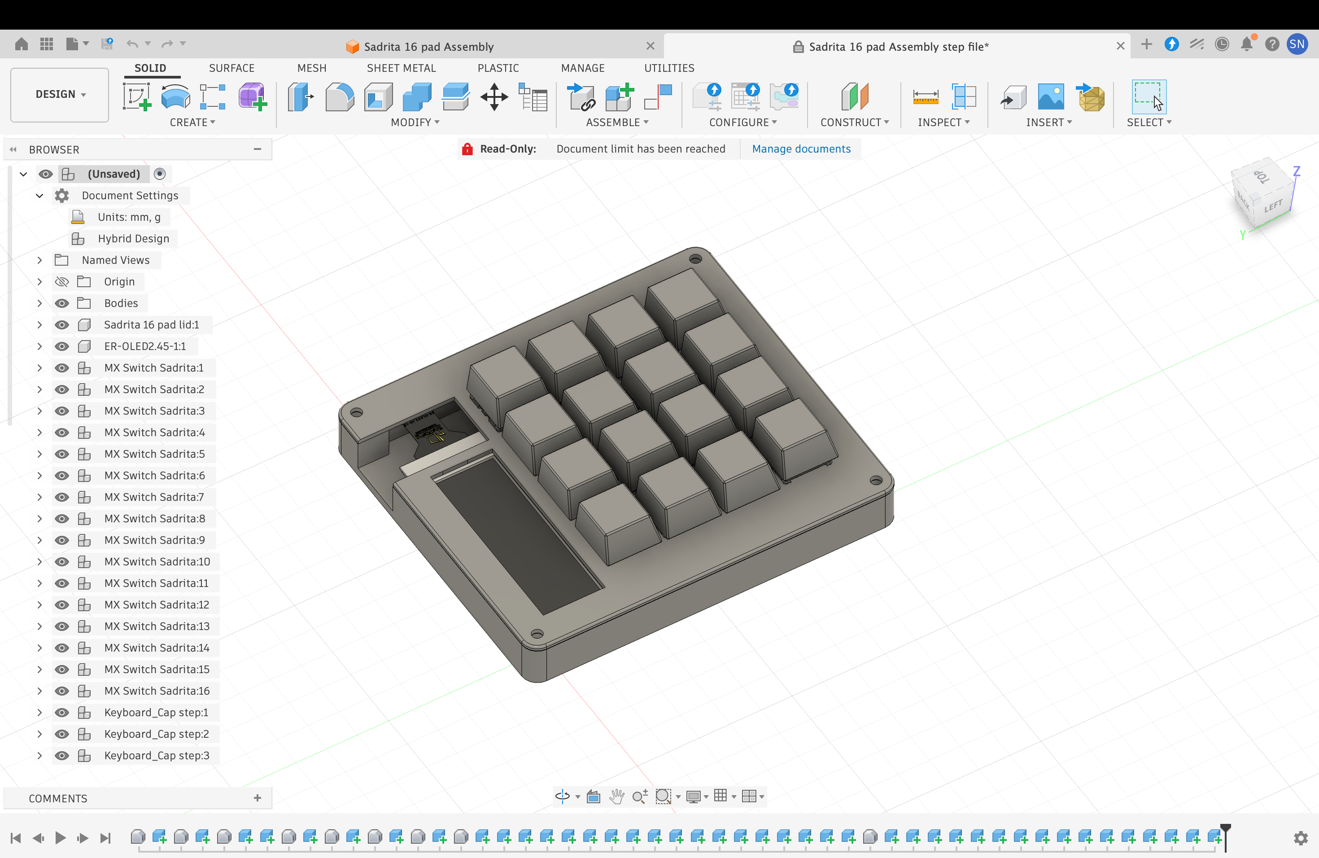
IMAGES/29.png
