Sadrita404/16-Key-Macro-Pad/IMAGES/30.png

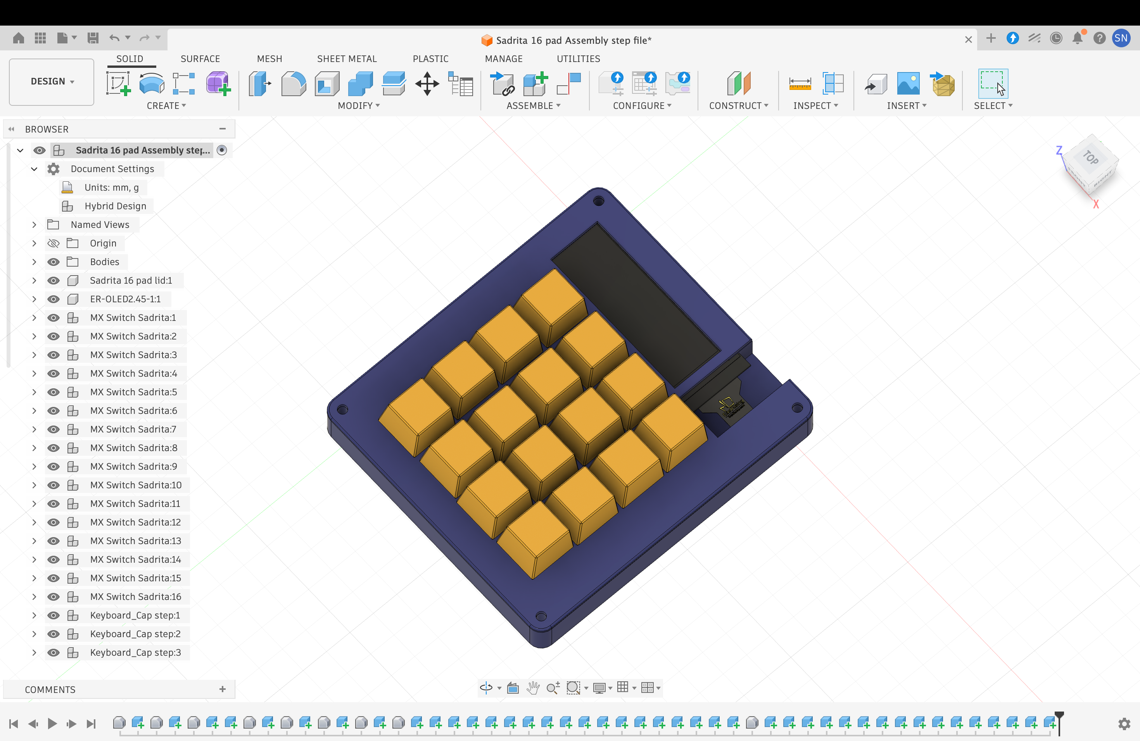
IMAGES/30.png
