Sadrita404/16-Key-Macro-Pad/IMAGES/31.png

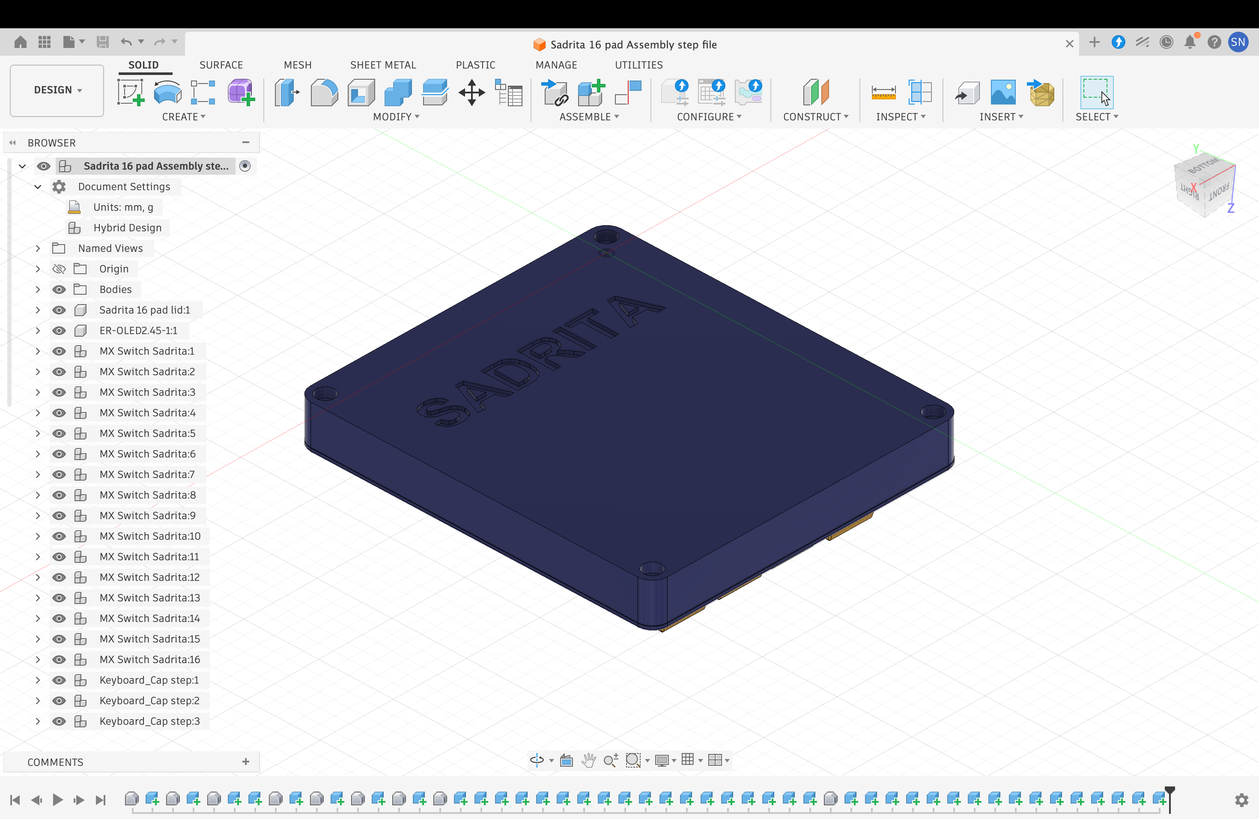
IMAGES/31.png
