Sadrita404/16-Key-Macro-Pad/IMAGES/32.png

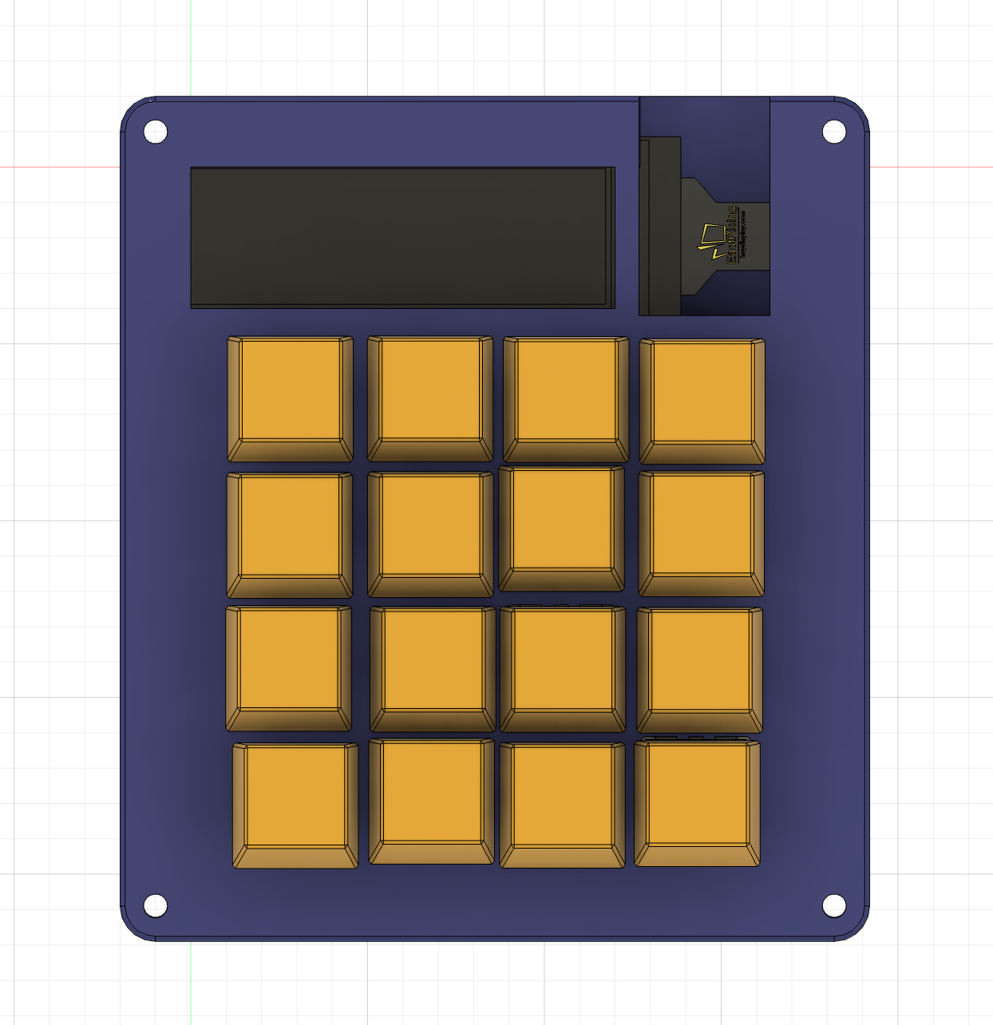
IMAGES/32.png
