Sadrita404/16-Key-Macro-Pad/IMAGES/33.png

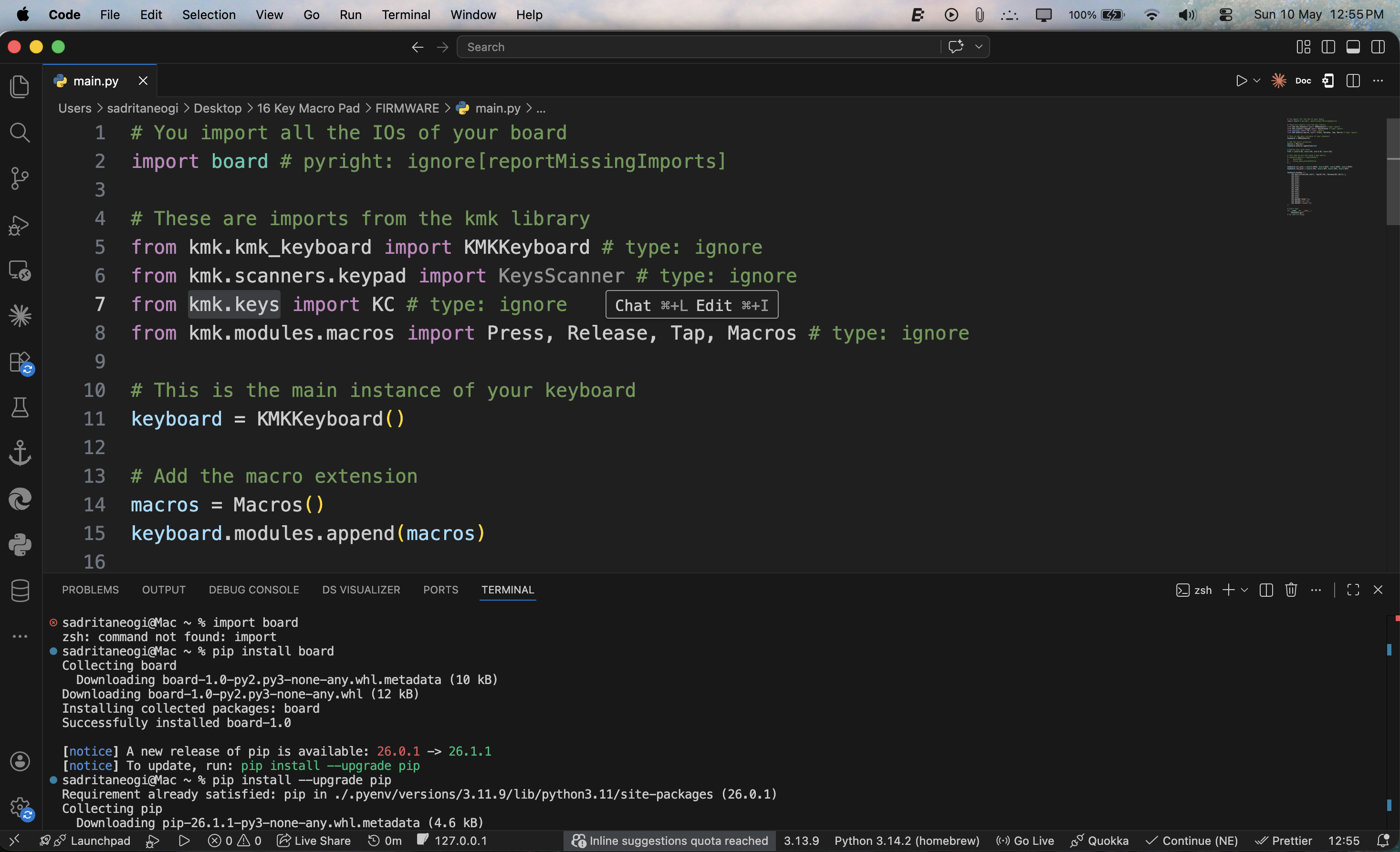
IMAGES/33.png
